MogleyC/Gentlman20211010/Etc/Doc/DM테크 블루투스 모듈/nrf52832_dm_rev3r1.pdf

## REVISION HISTORY

## REV1.0

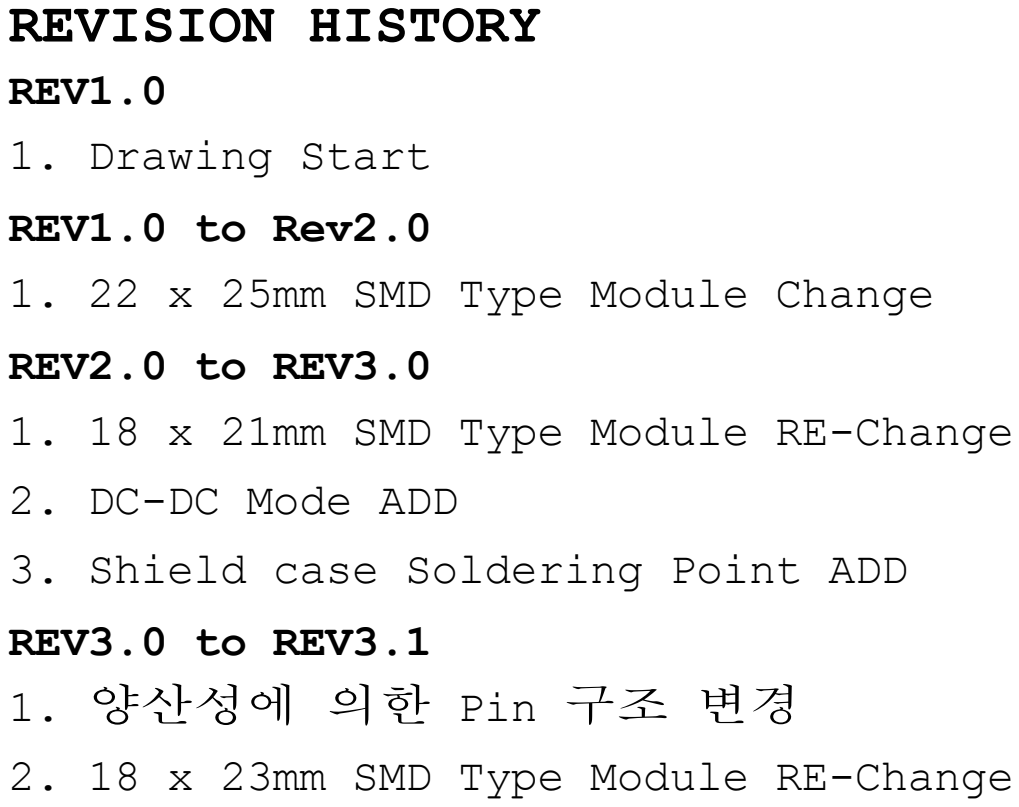
[picture p1: page 1]
Title; Size; Document Number; Rev; Date:; Sheet; <Doc>; nRF52832_DM Module; Tuesday, March 02, 2021

1. Drawing Start
REV1.0 to Rev2.0
1. 22 x 25mm SMD Type Module Change
REV2.0 to REV3.0
1. 18 x 21mm SMD Type Module RE-Change

2. DC-DC Mode ADD

3. Shield case Soldering Point ADD
REV3.0 to REV3.1
1. 양산성에 의한 Pin 구조 변경

2. 18 x 23mm SMD Type Module RE-Change

DMTech.Co.,Ltd.

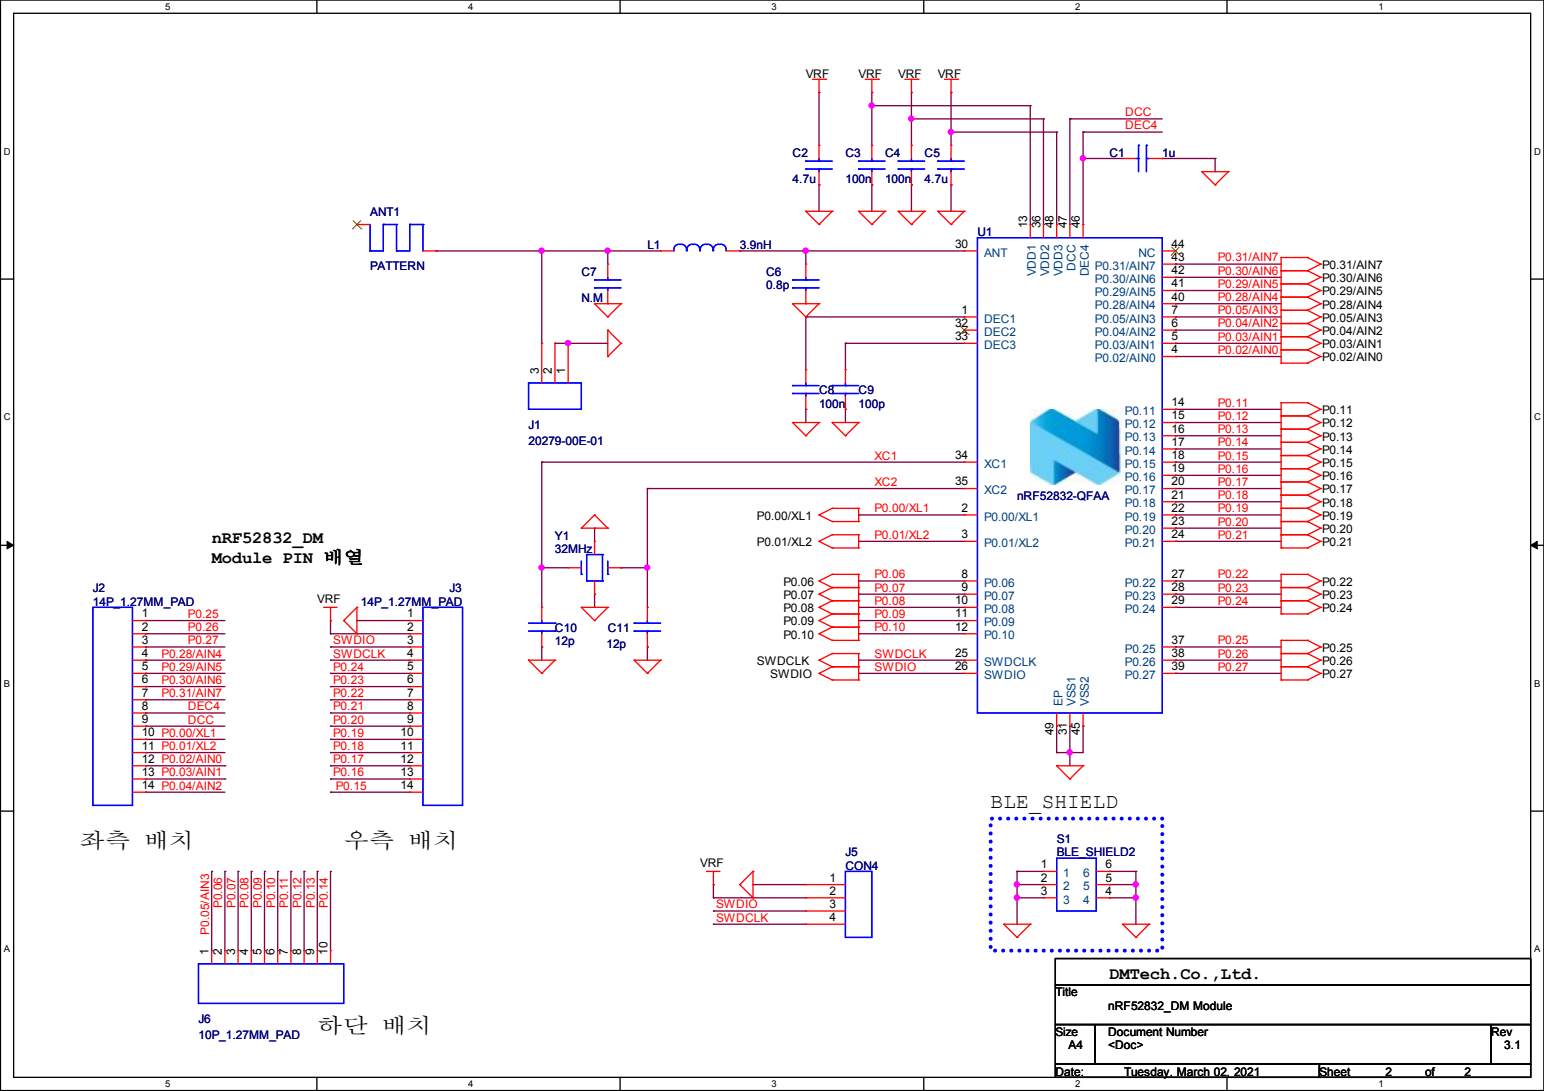
[picture p2: page 2]
