MogleyC/Gentlman20211010/Etc/Doc/nRF-DK/nRF52810 Reference circuitry.pdf

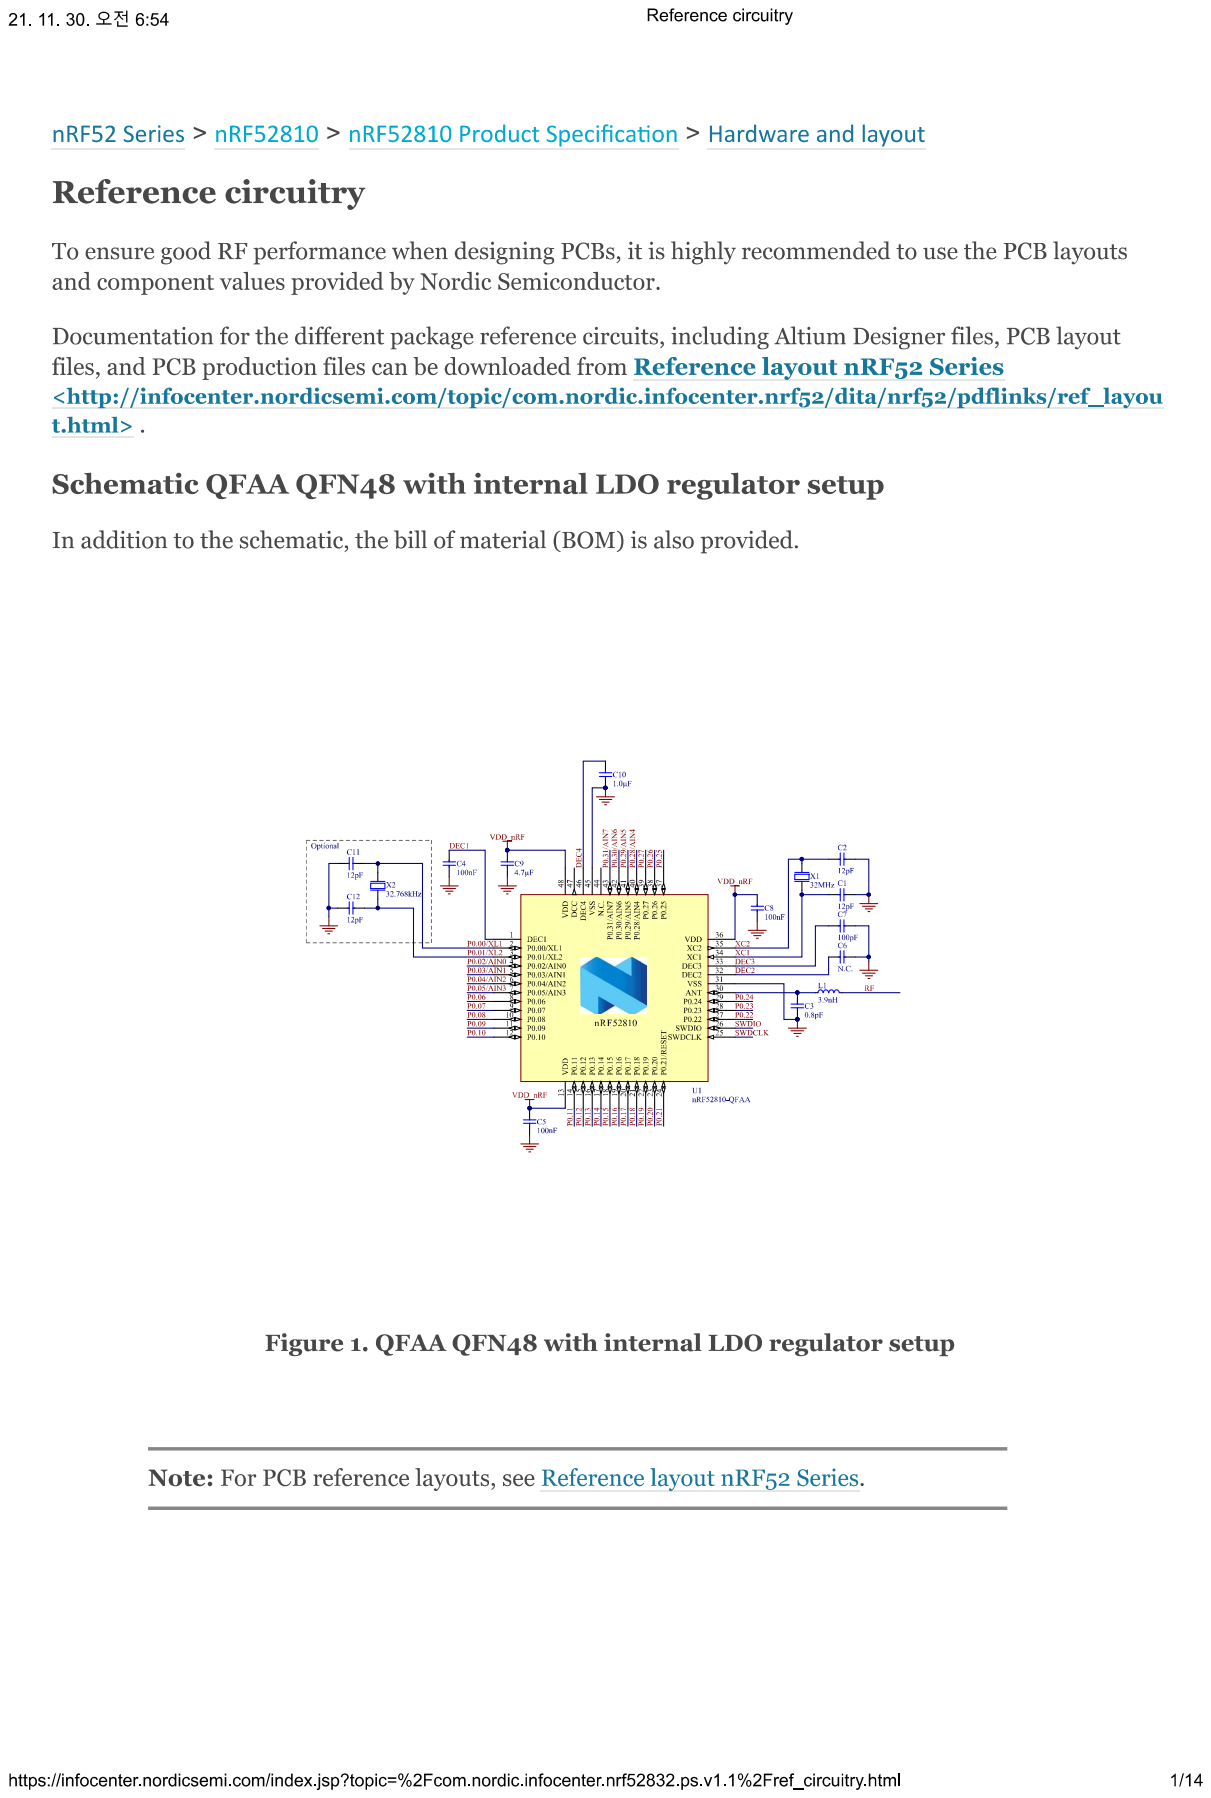
[picture p4: page 1]

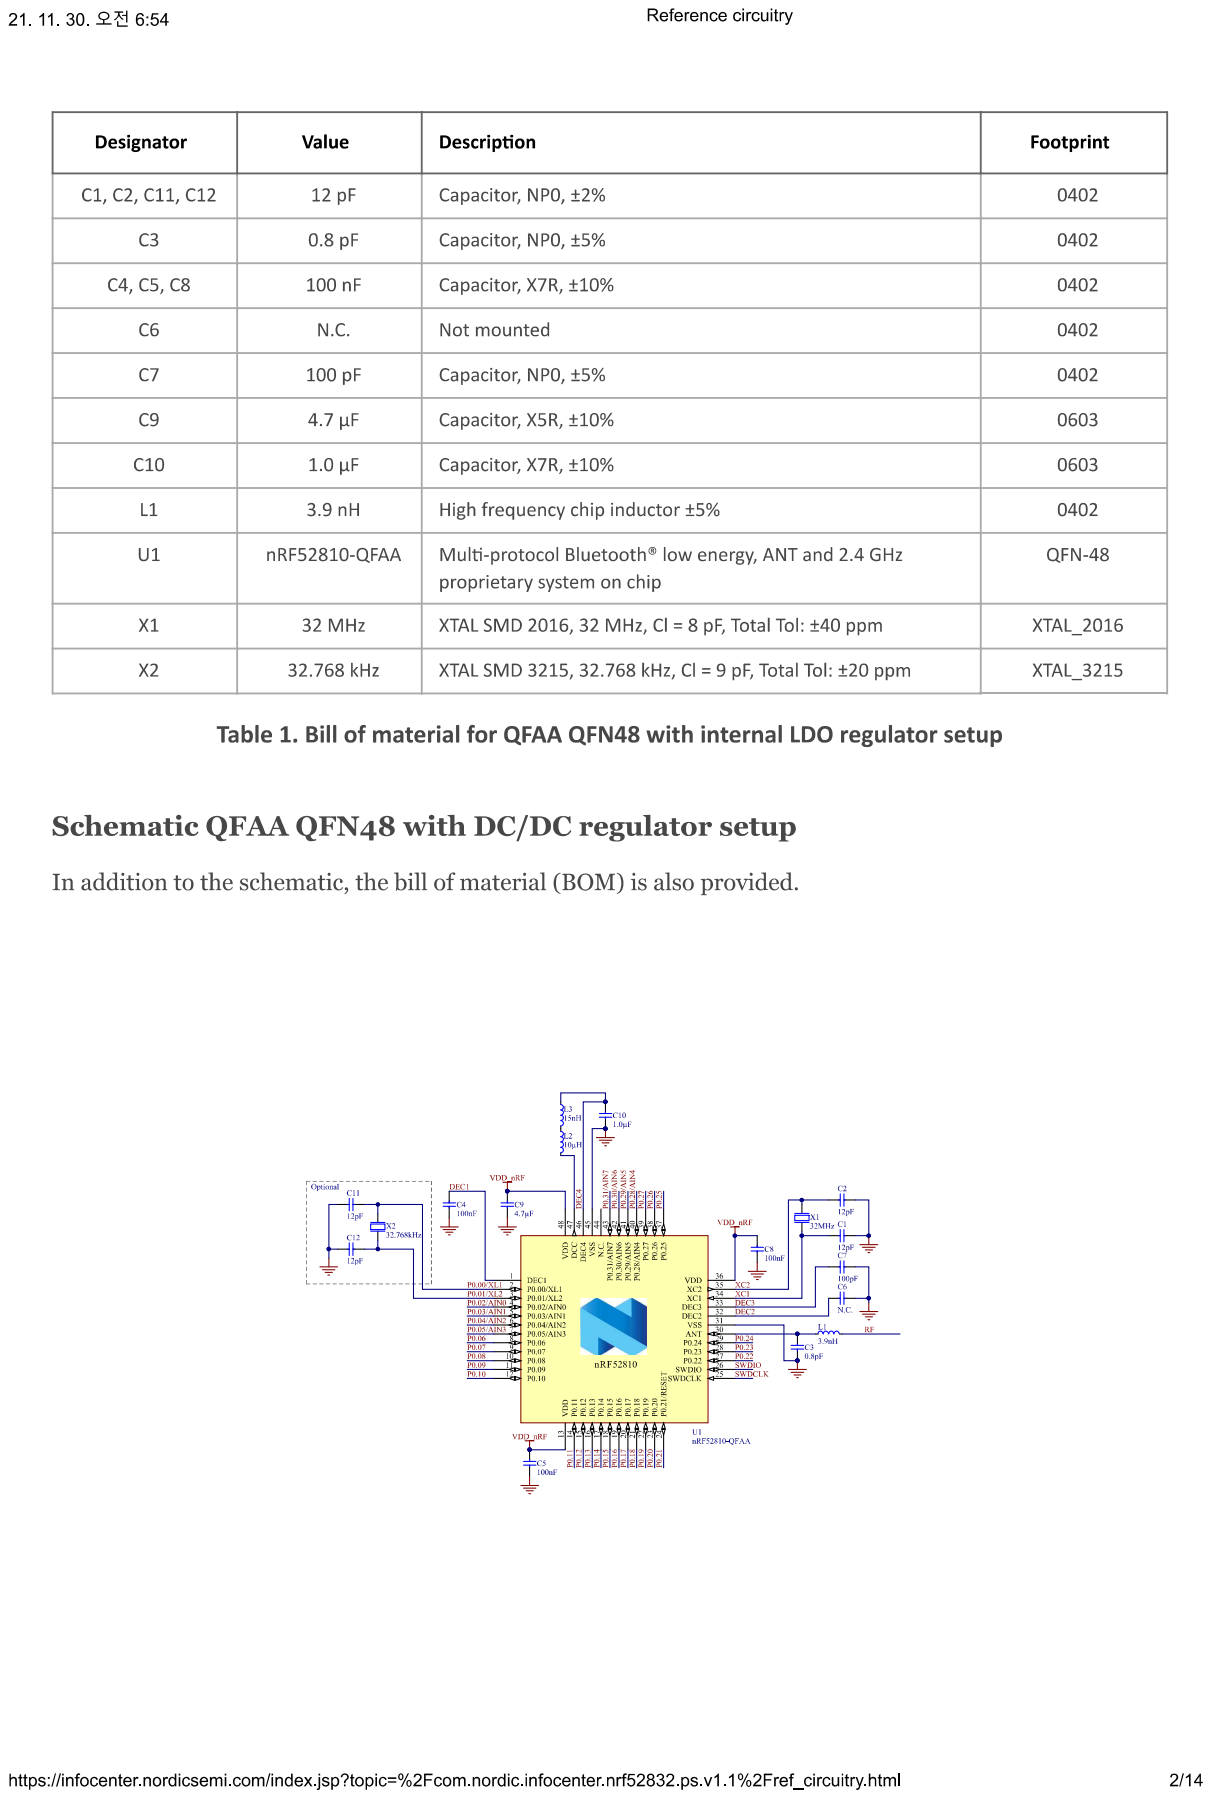
[picture p5: page 2]

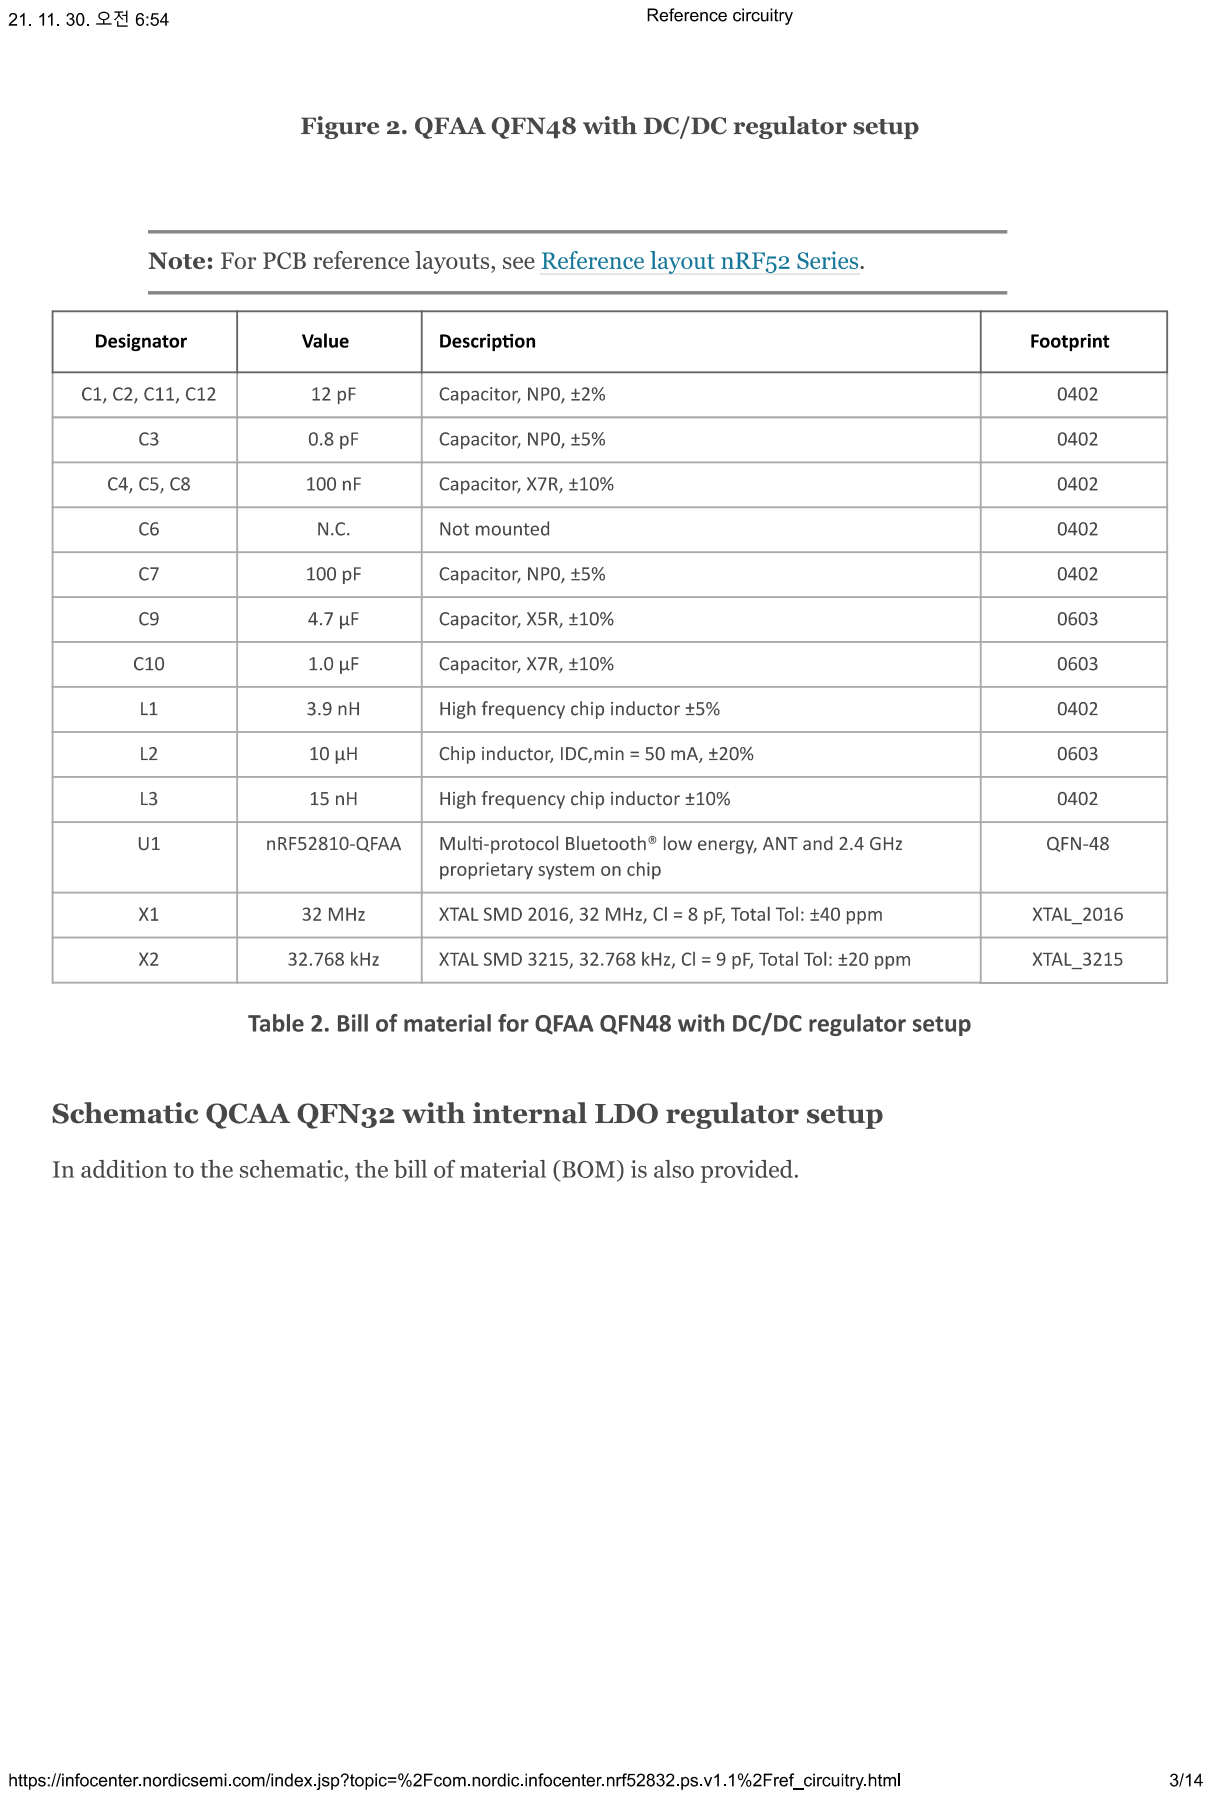
[picture p6: page 3]

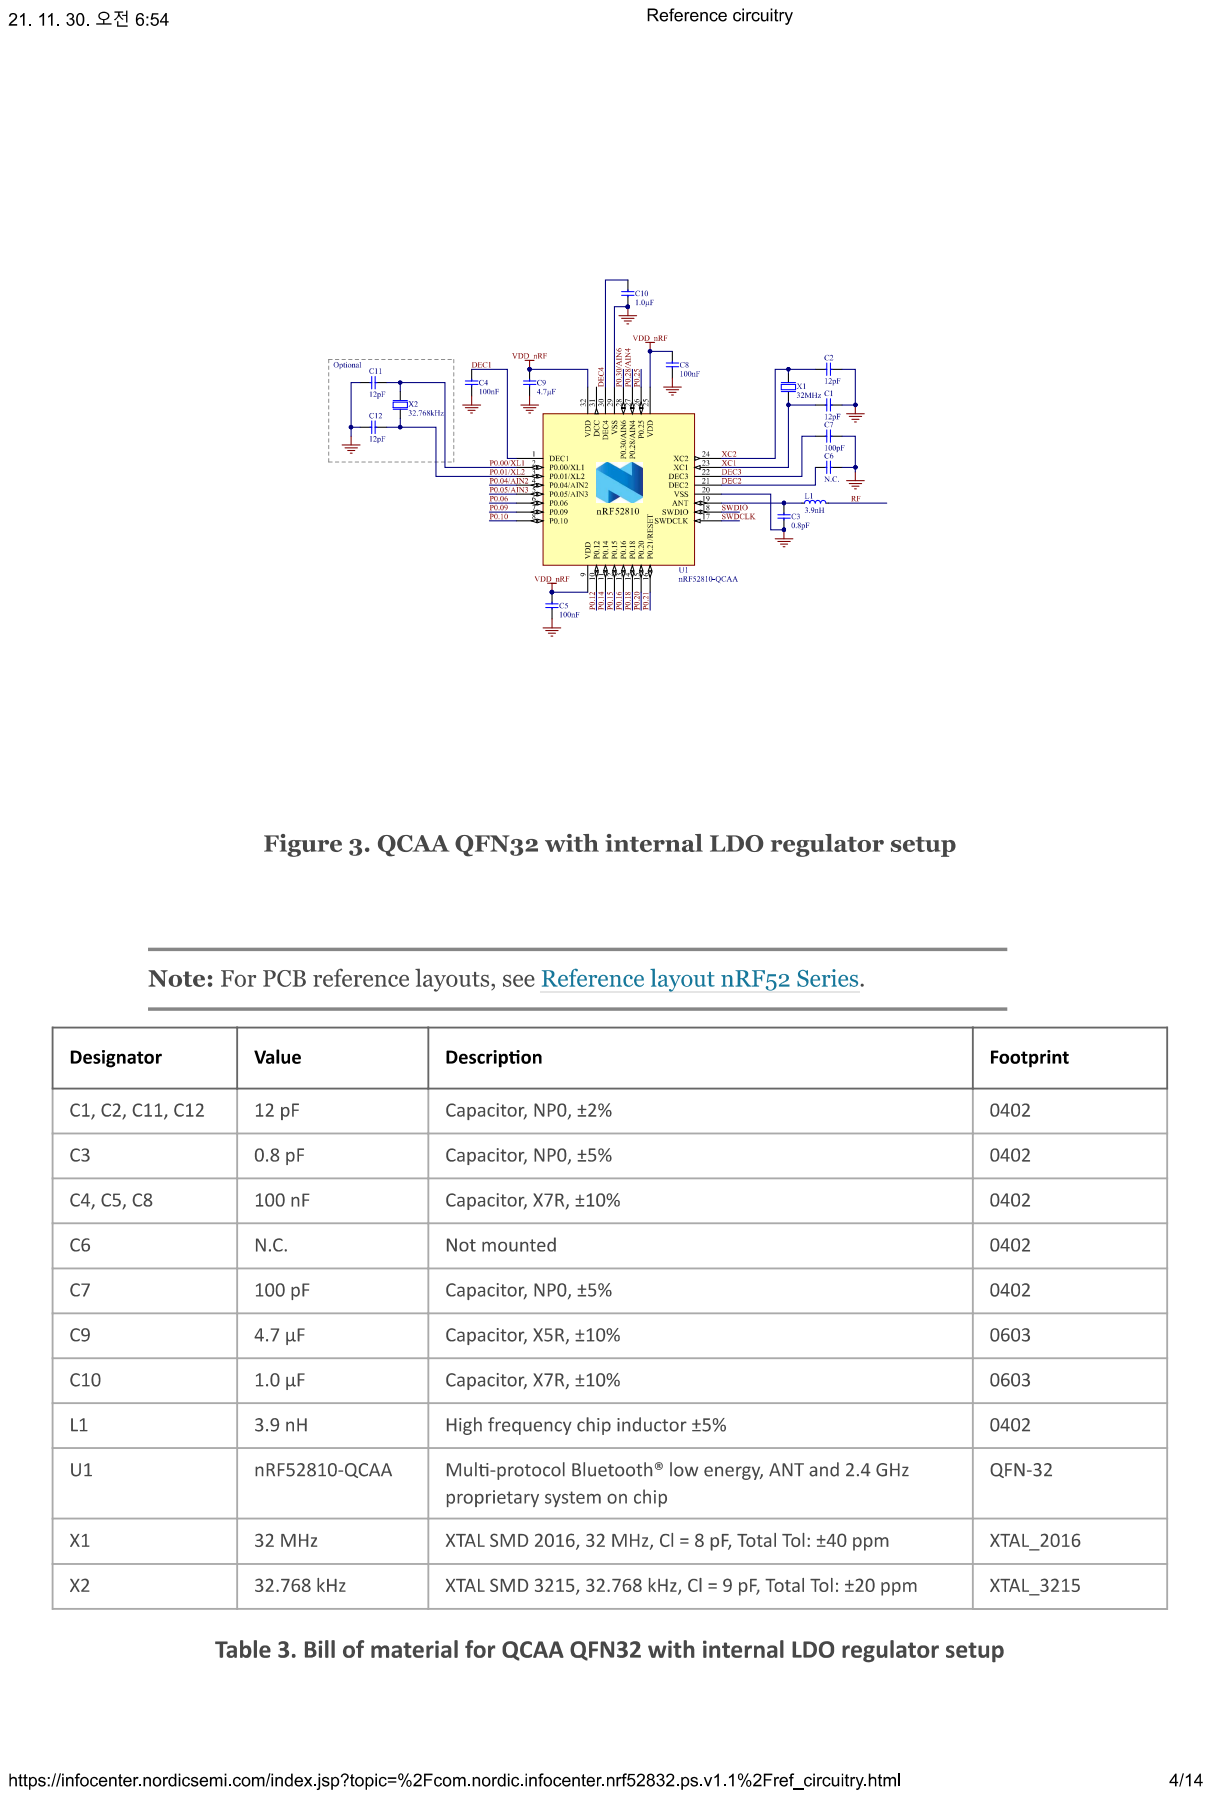
[picture p7: page 4]

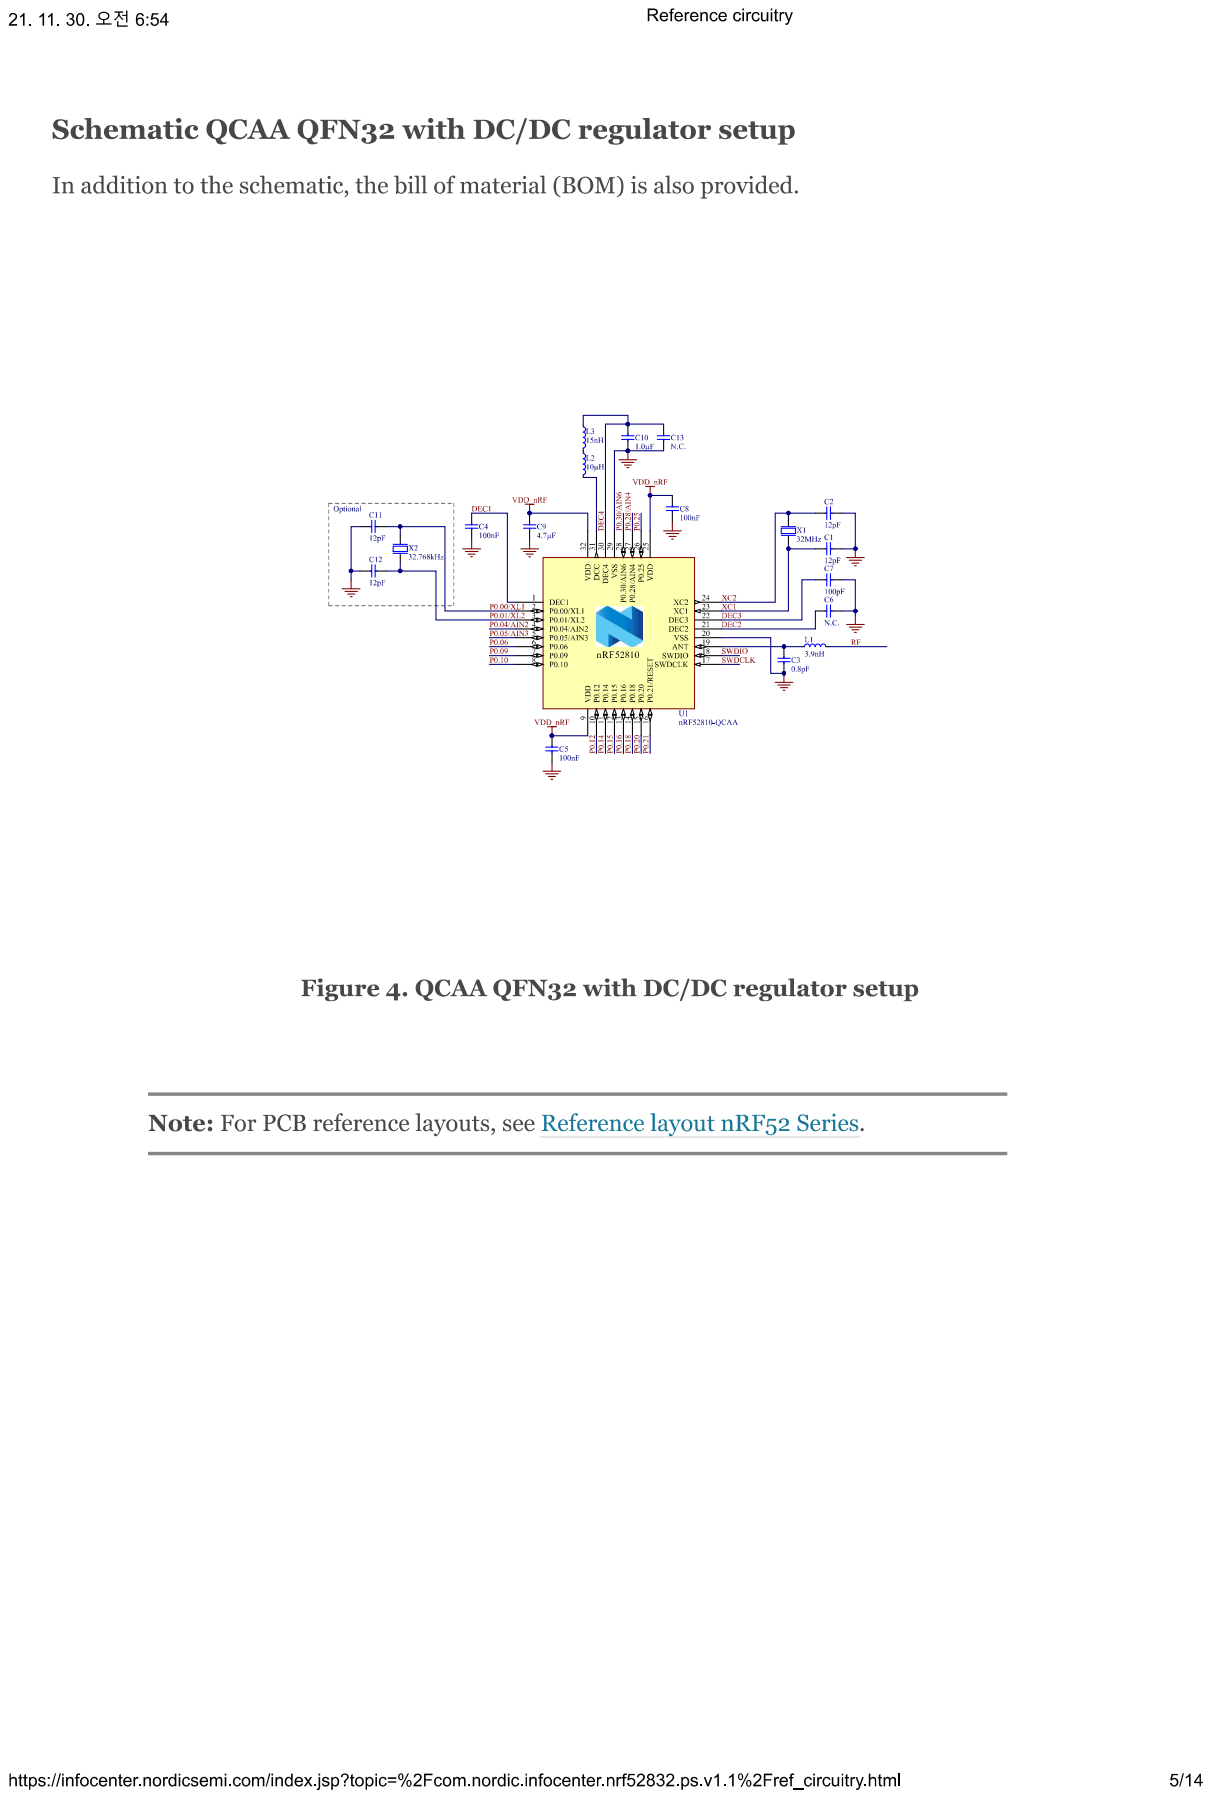
[picture p8: page 5]

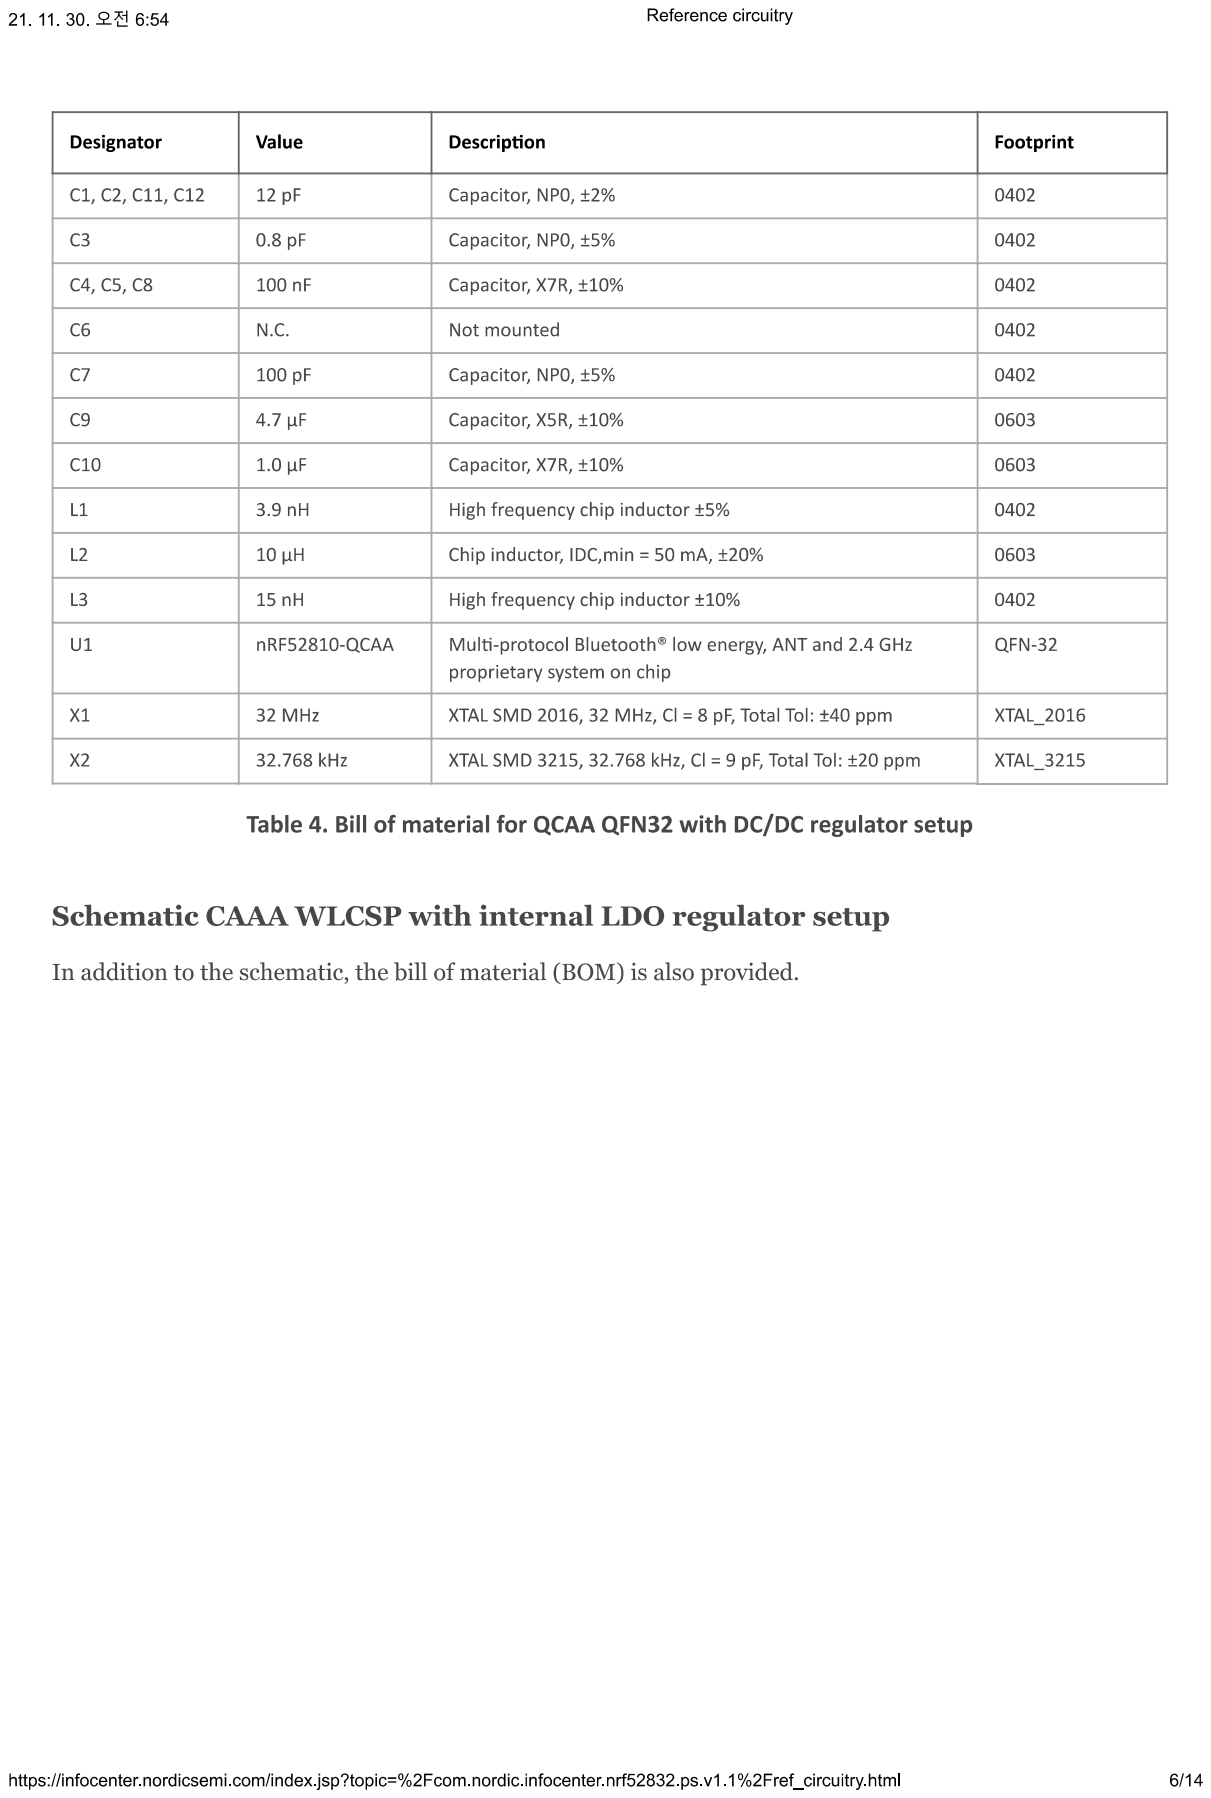
[picture p9: page 6]

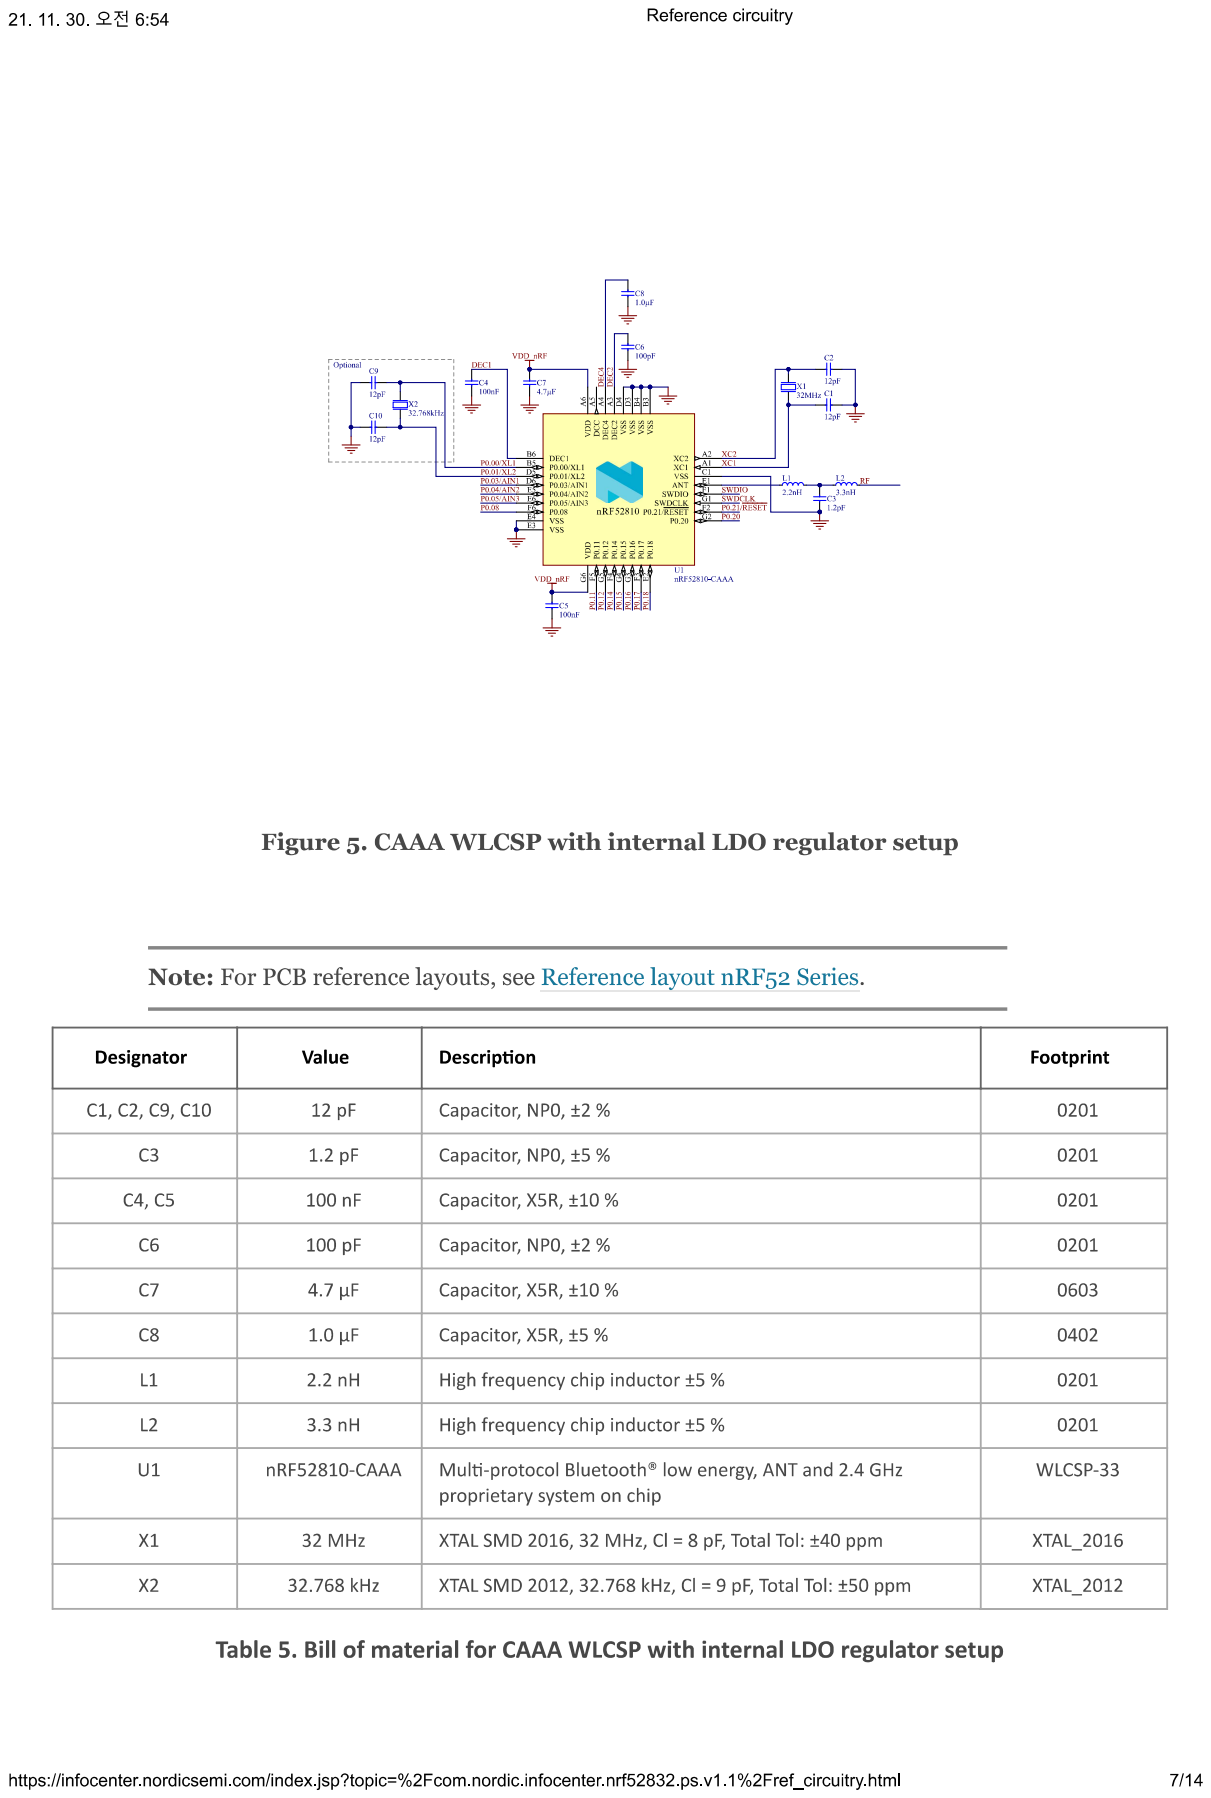
[picture p10: page 7]

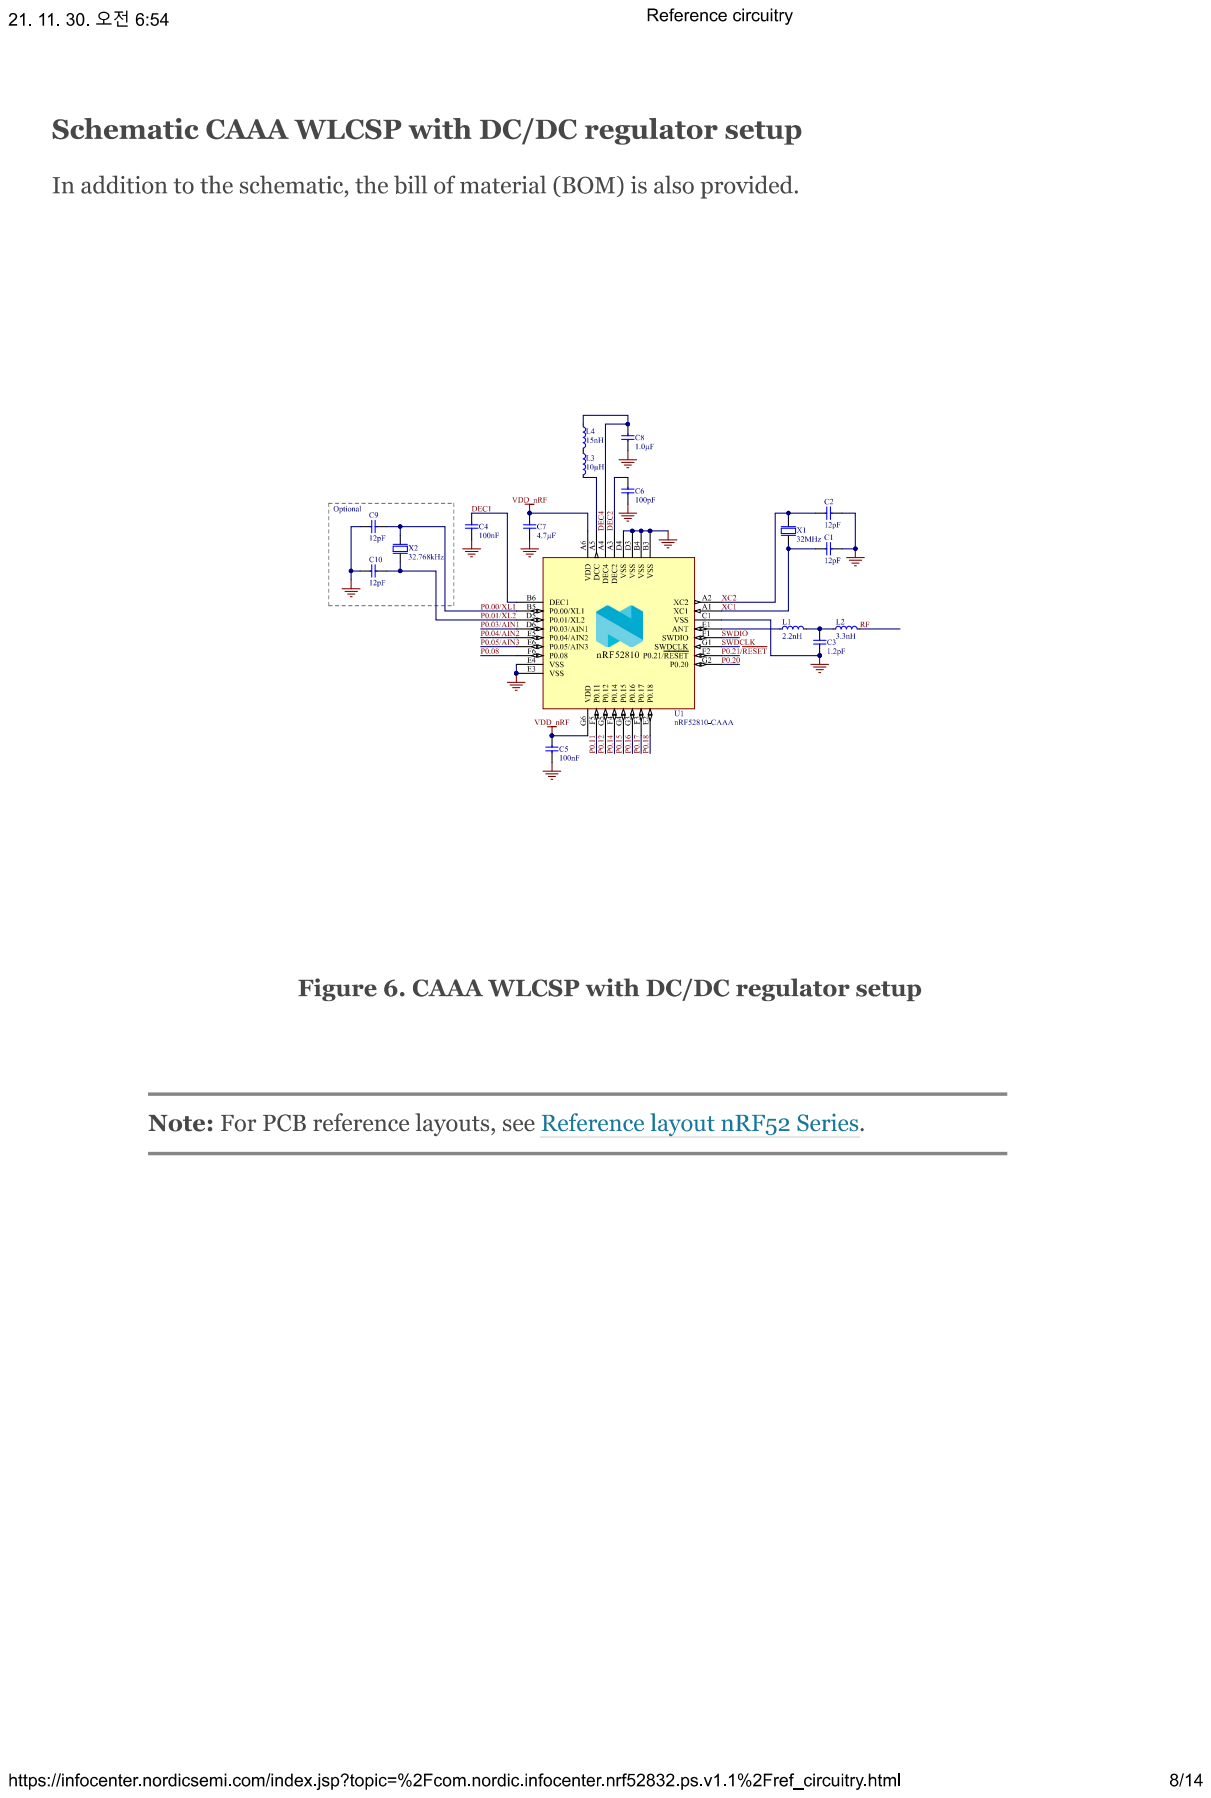
[picture p11: page 8]

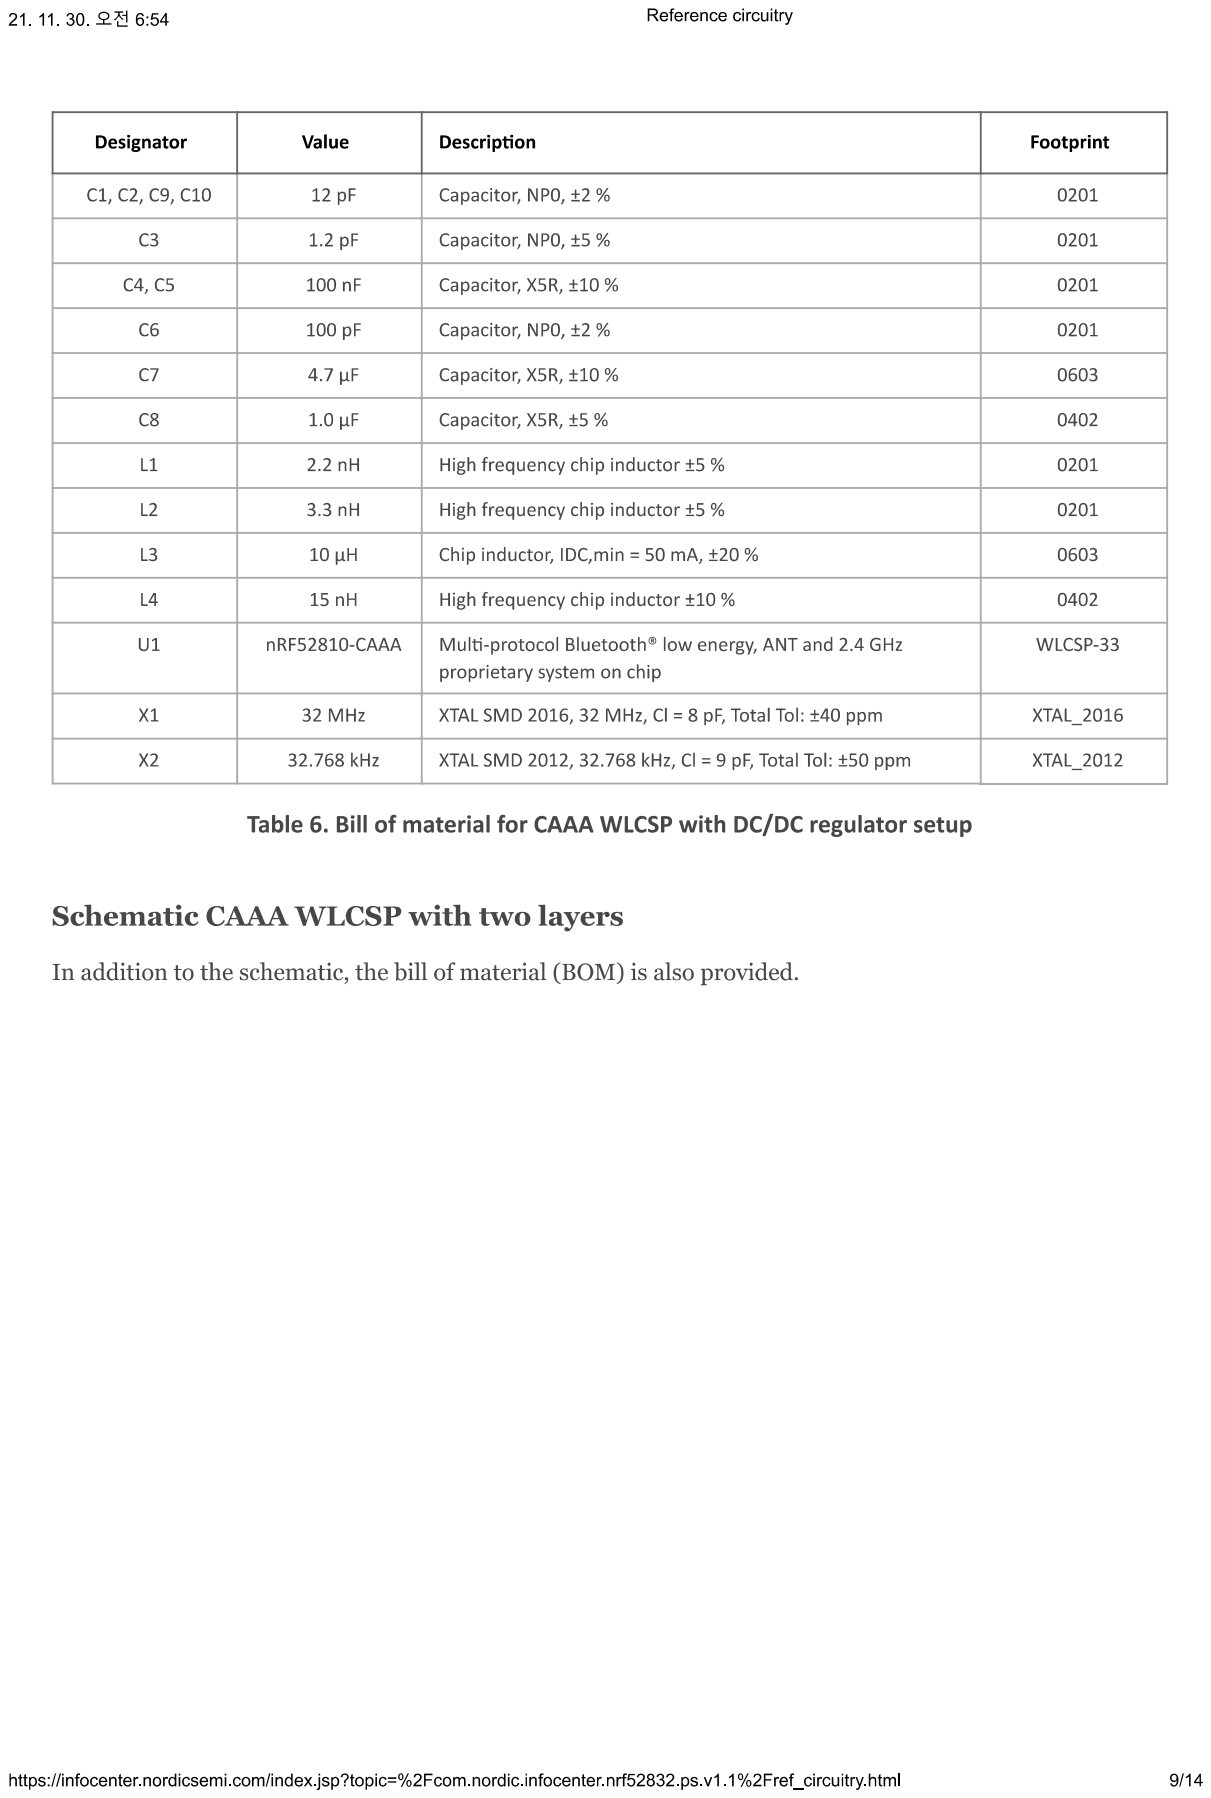
[picture p12: page 9]

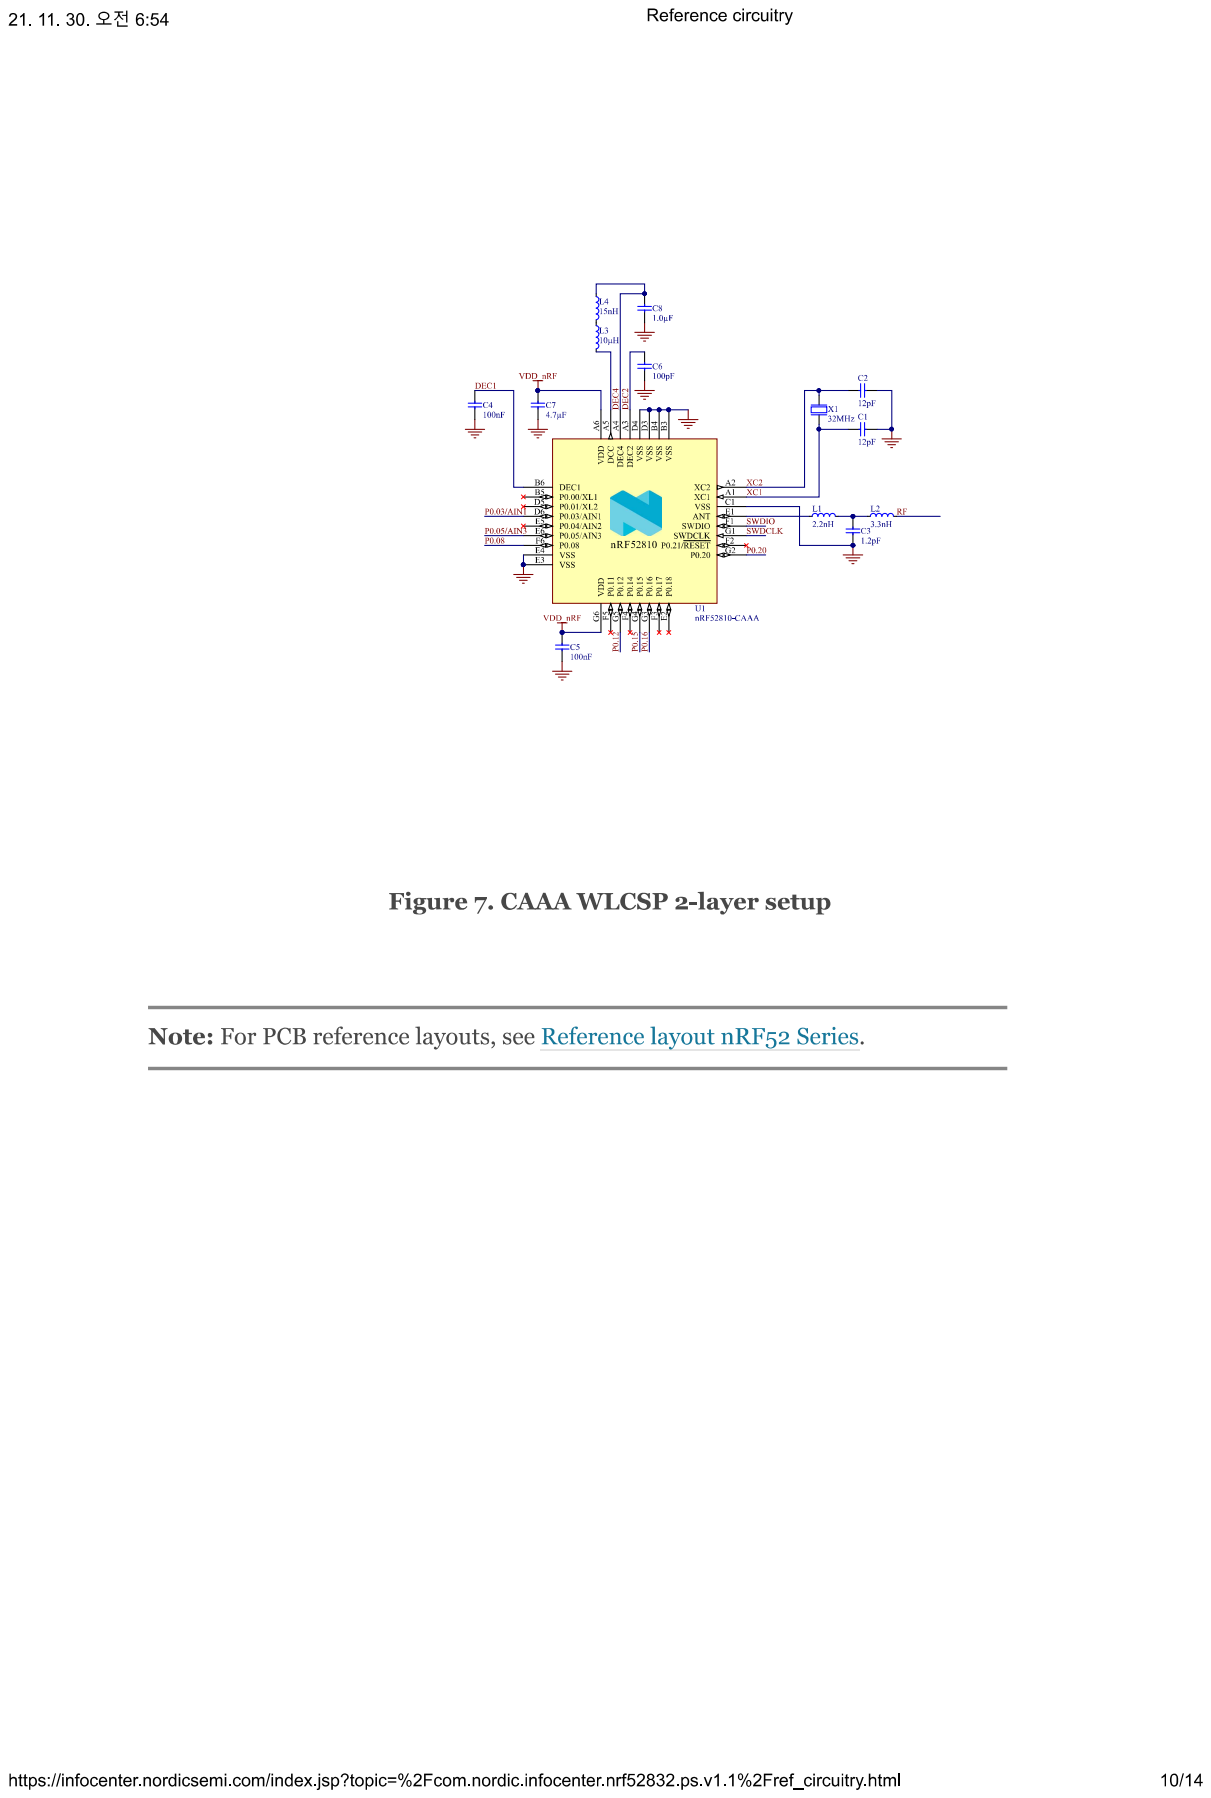
[picture p13: page 10]

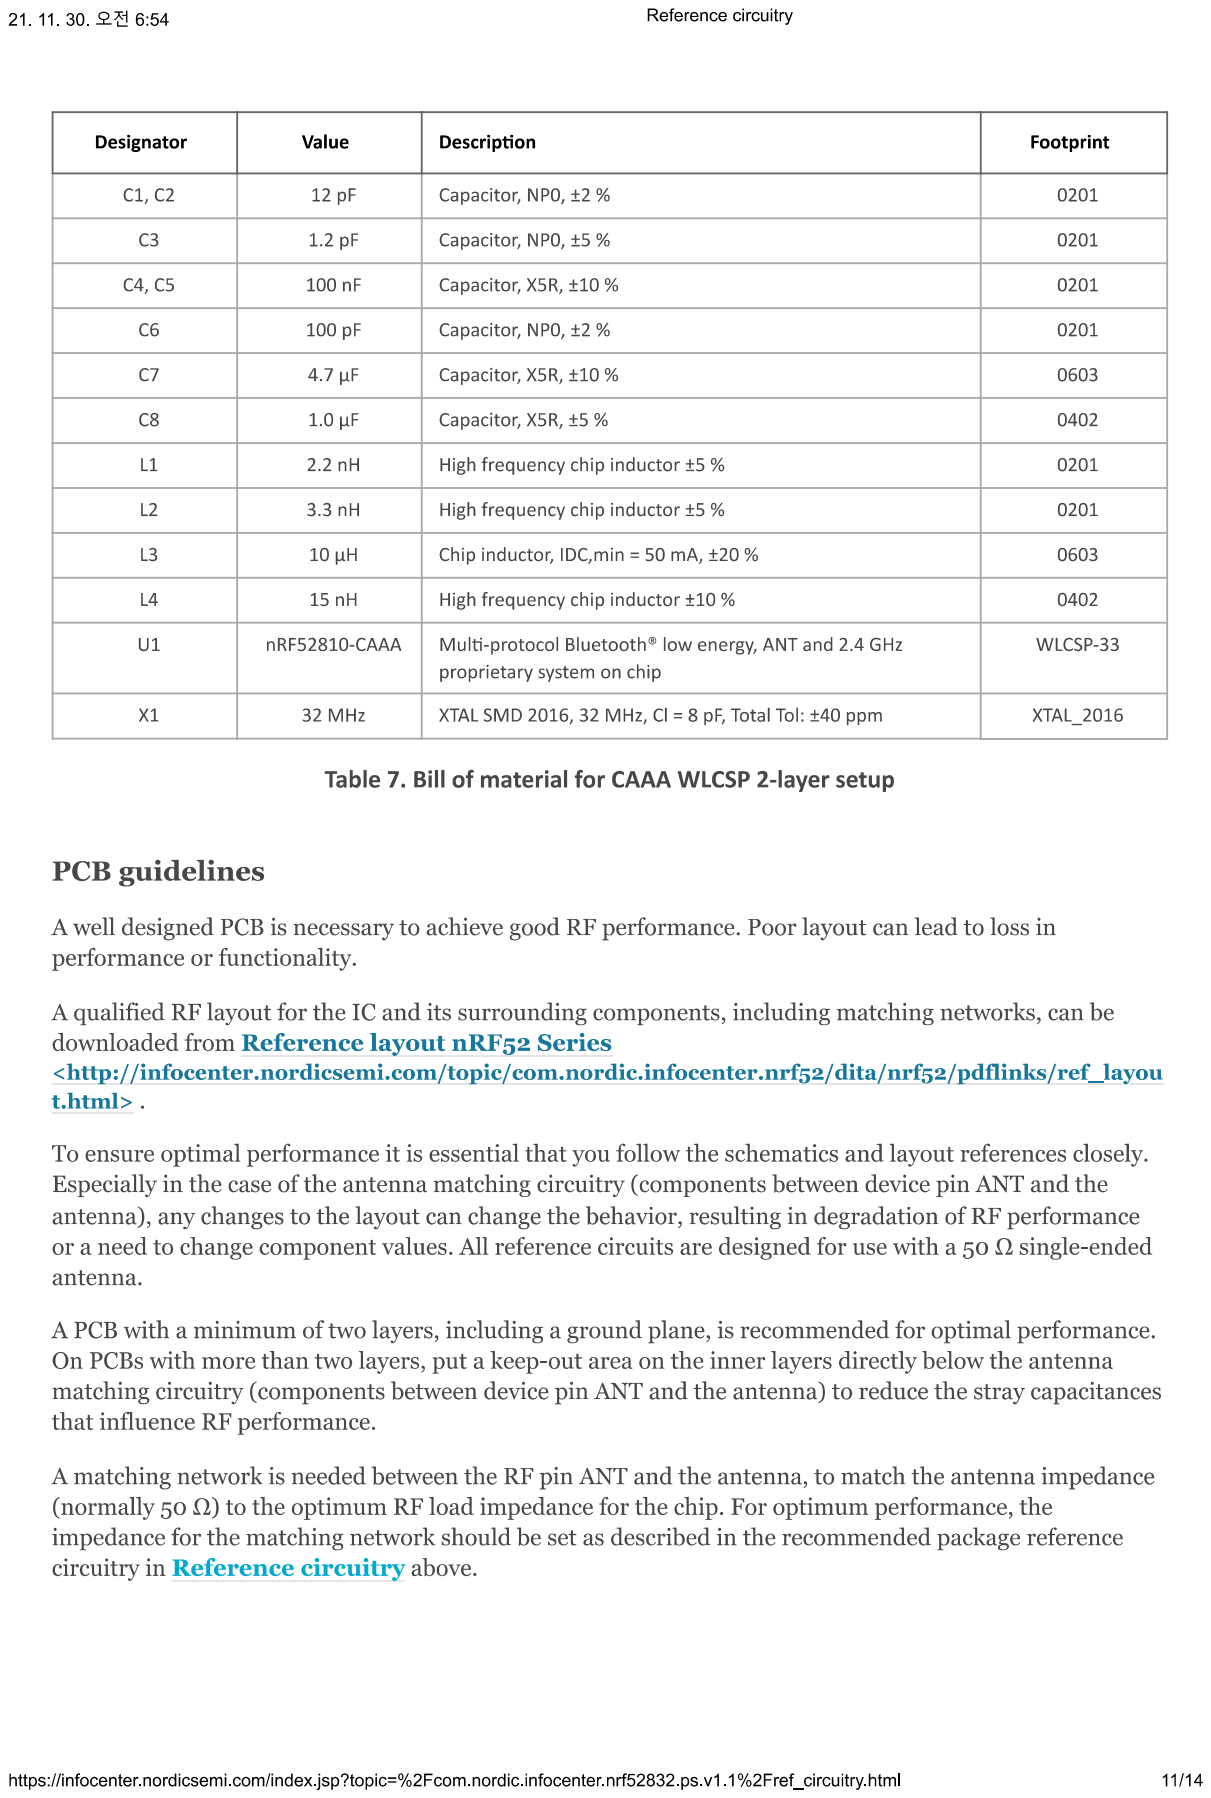
[picture p14: page 11]

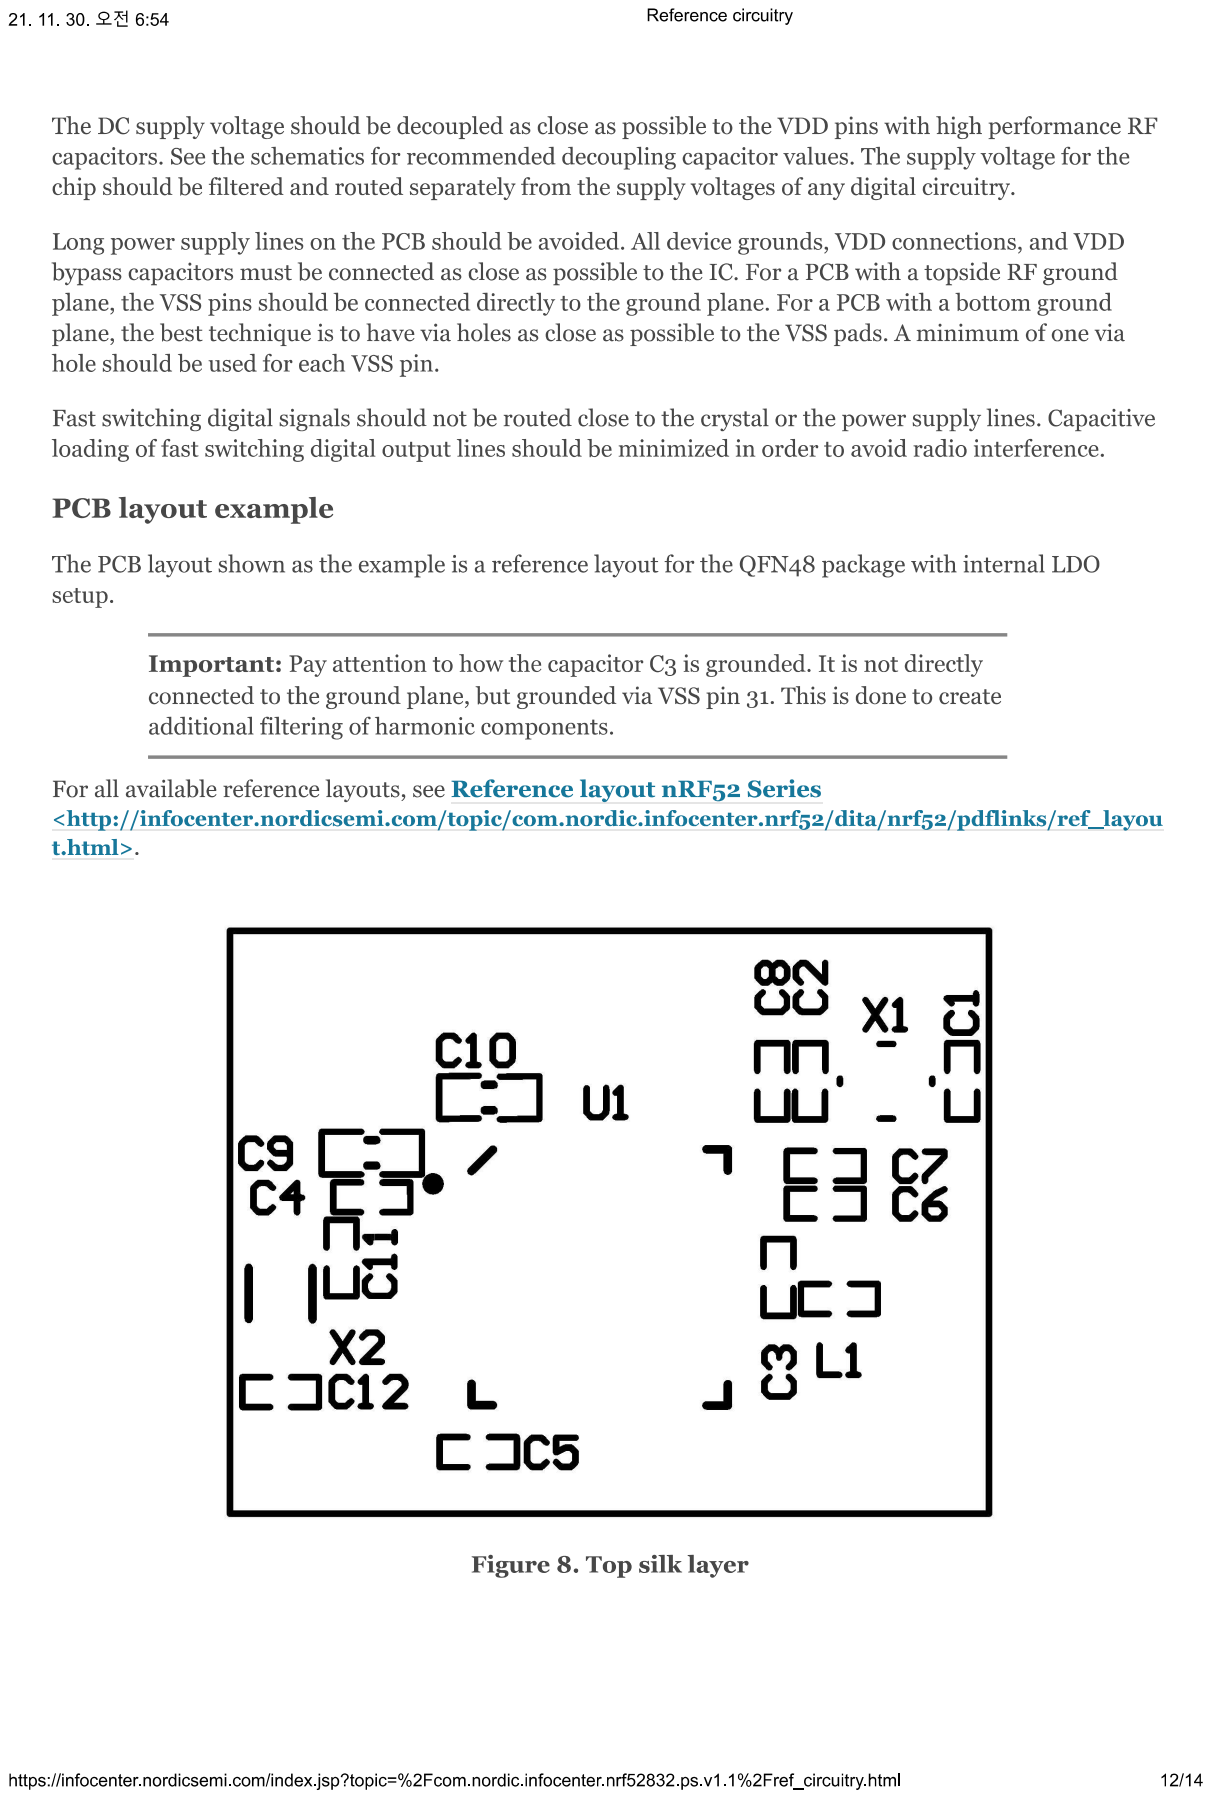
[picture p15: page 12]

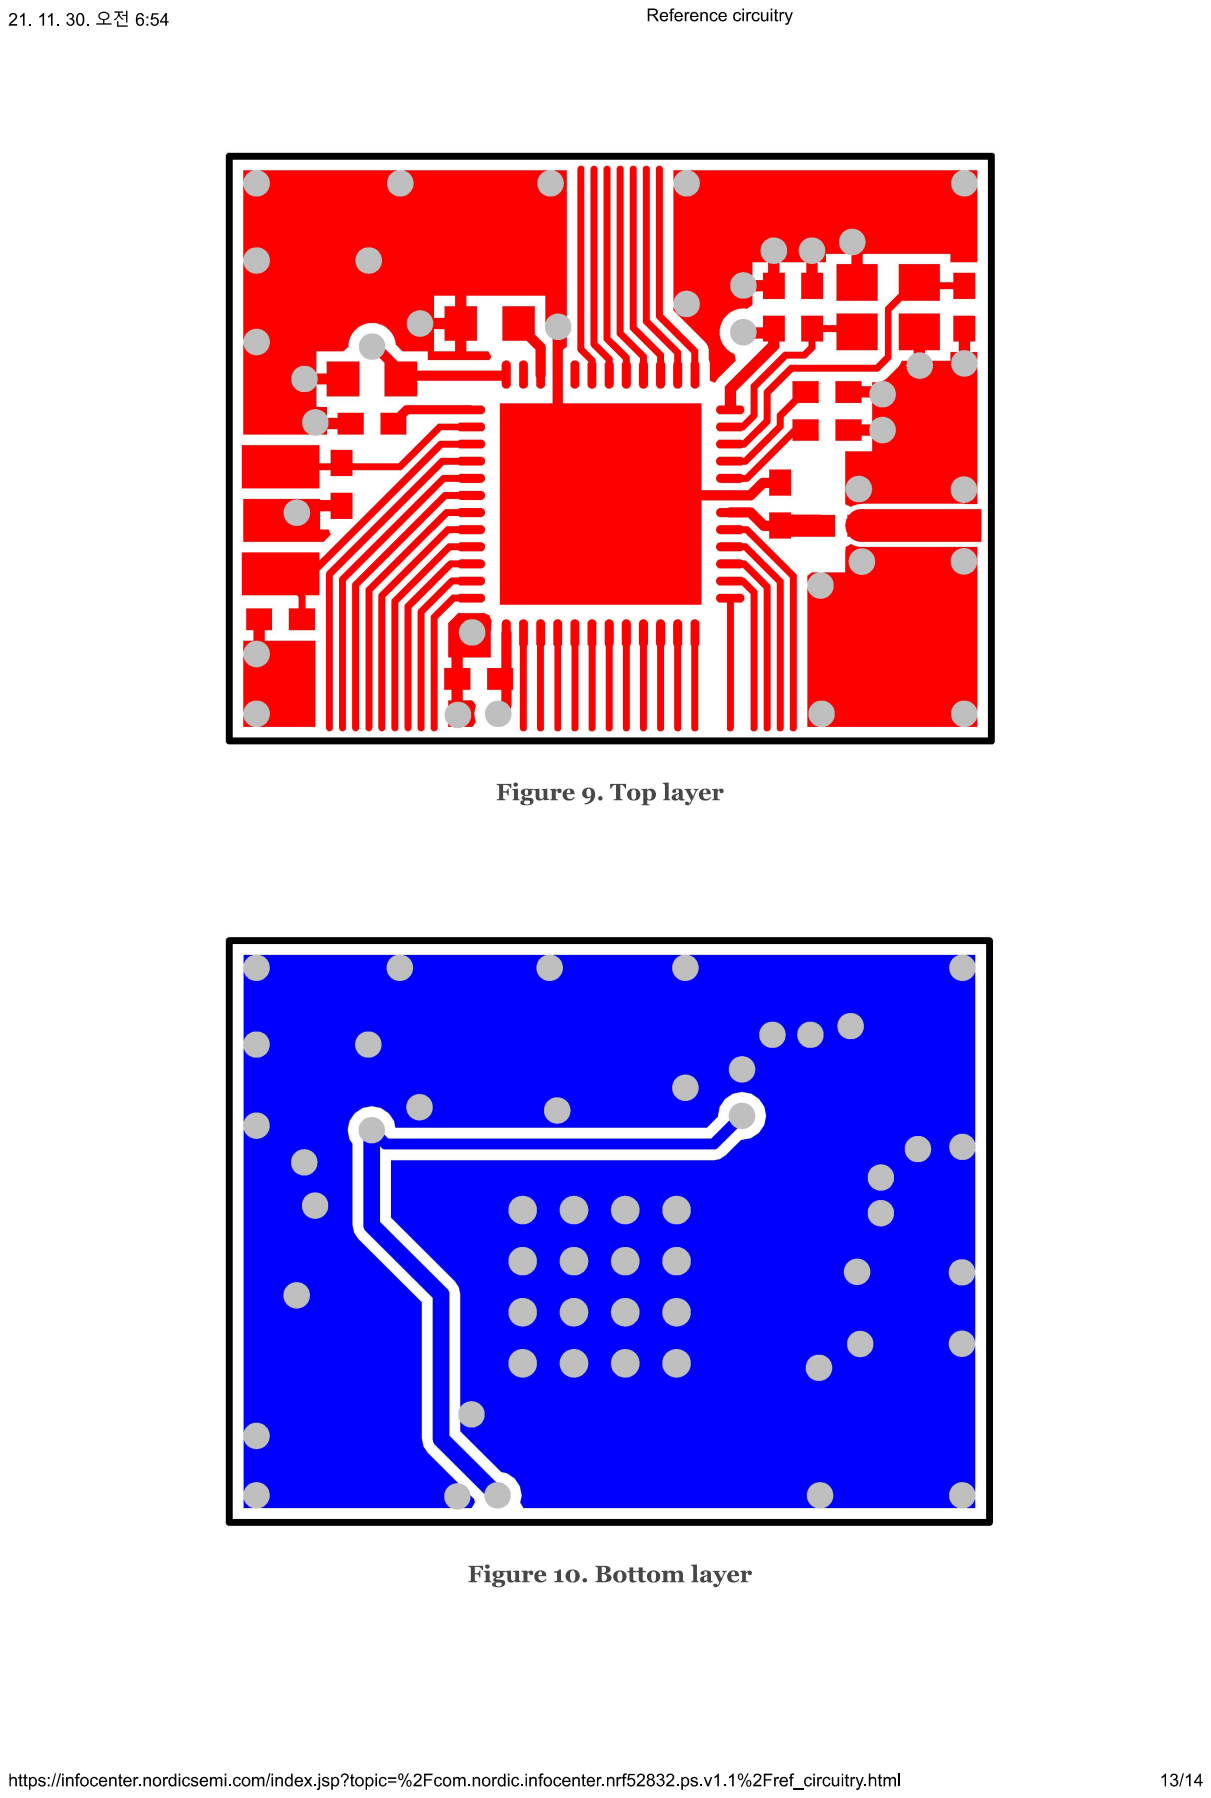
[picture p16: page 13]

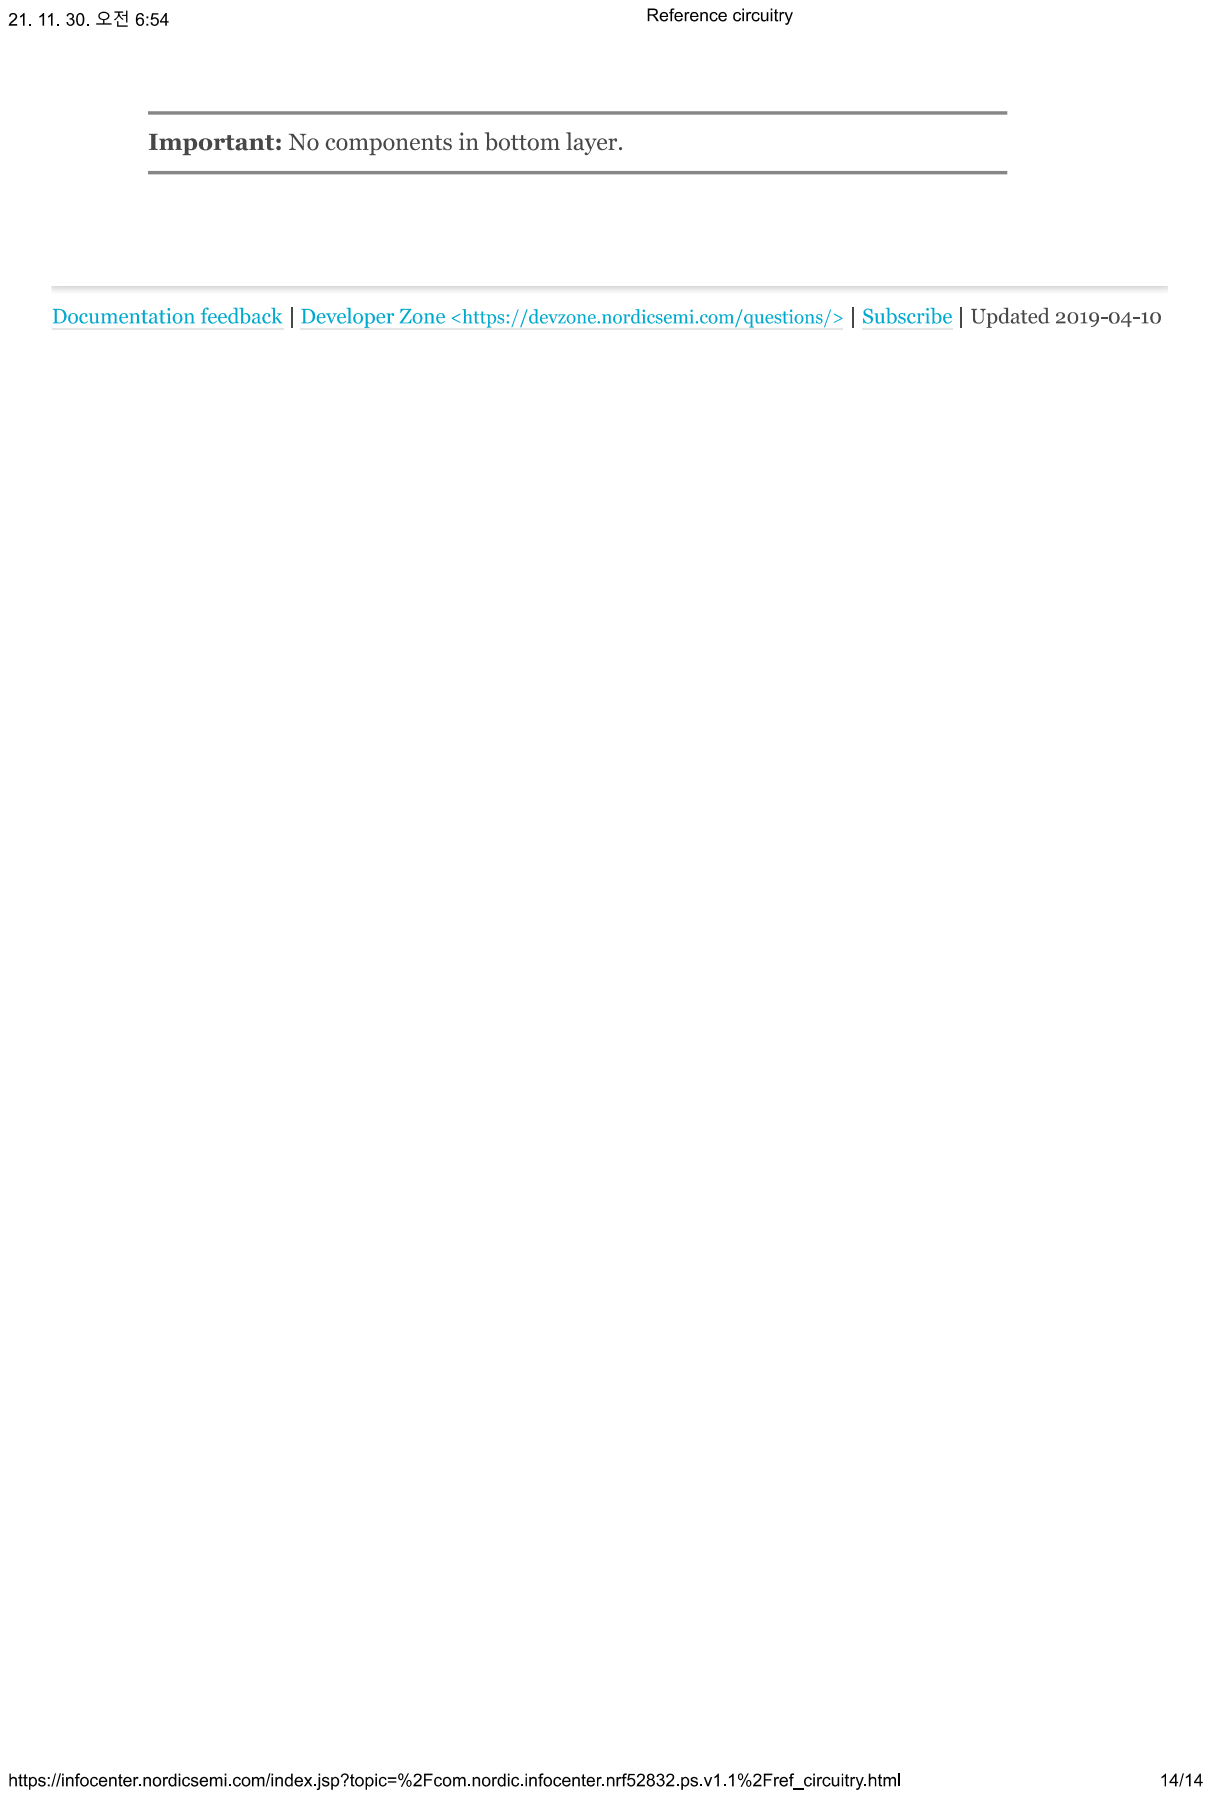
[picture p17: page 14]
