MogleyC/Gentlman20211010/KiCAD/KiCAD_Gentlman_V5.3/Dataseets/V5.2/201228 CPP-093AB(demo2).PDF

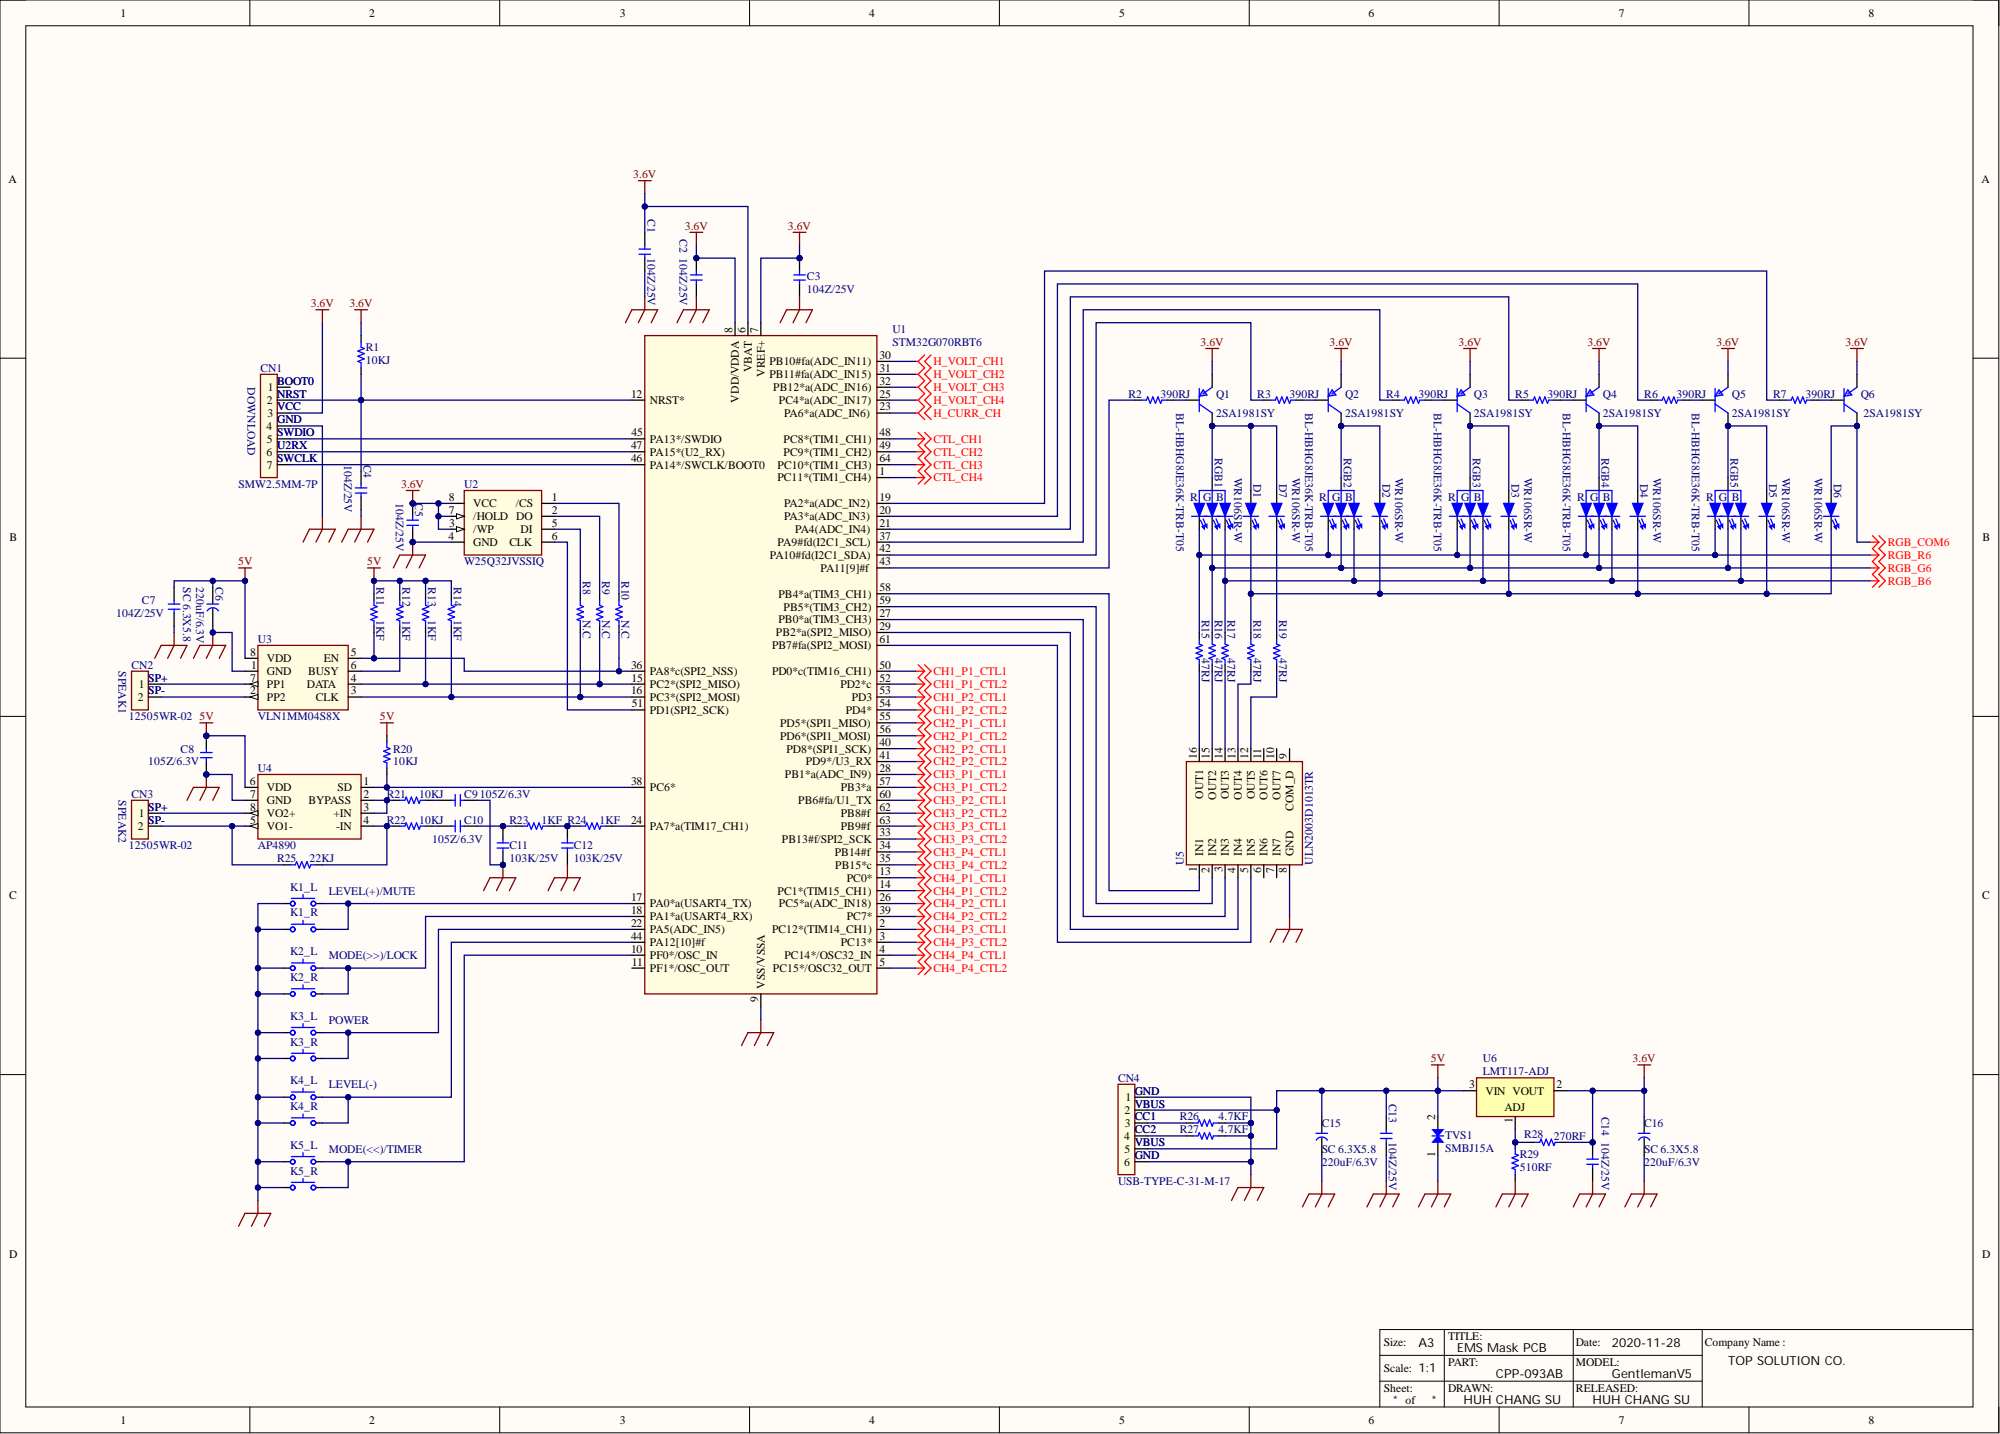
[picture p18: page 1]

U 2RX | | 4
K | 4 6

5 9
2 7
2 9
6 1

1 8 | | 3 9
2 2 | | 2
4 4 | | 3

D E(>>)/ L OCK | | 1 0

R2 6 4.7 KF
R2 4.7 | KF

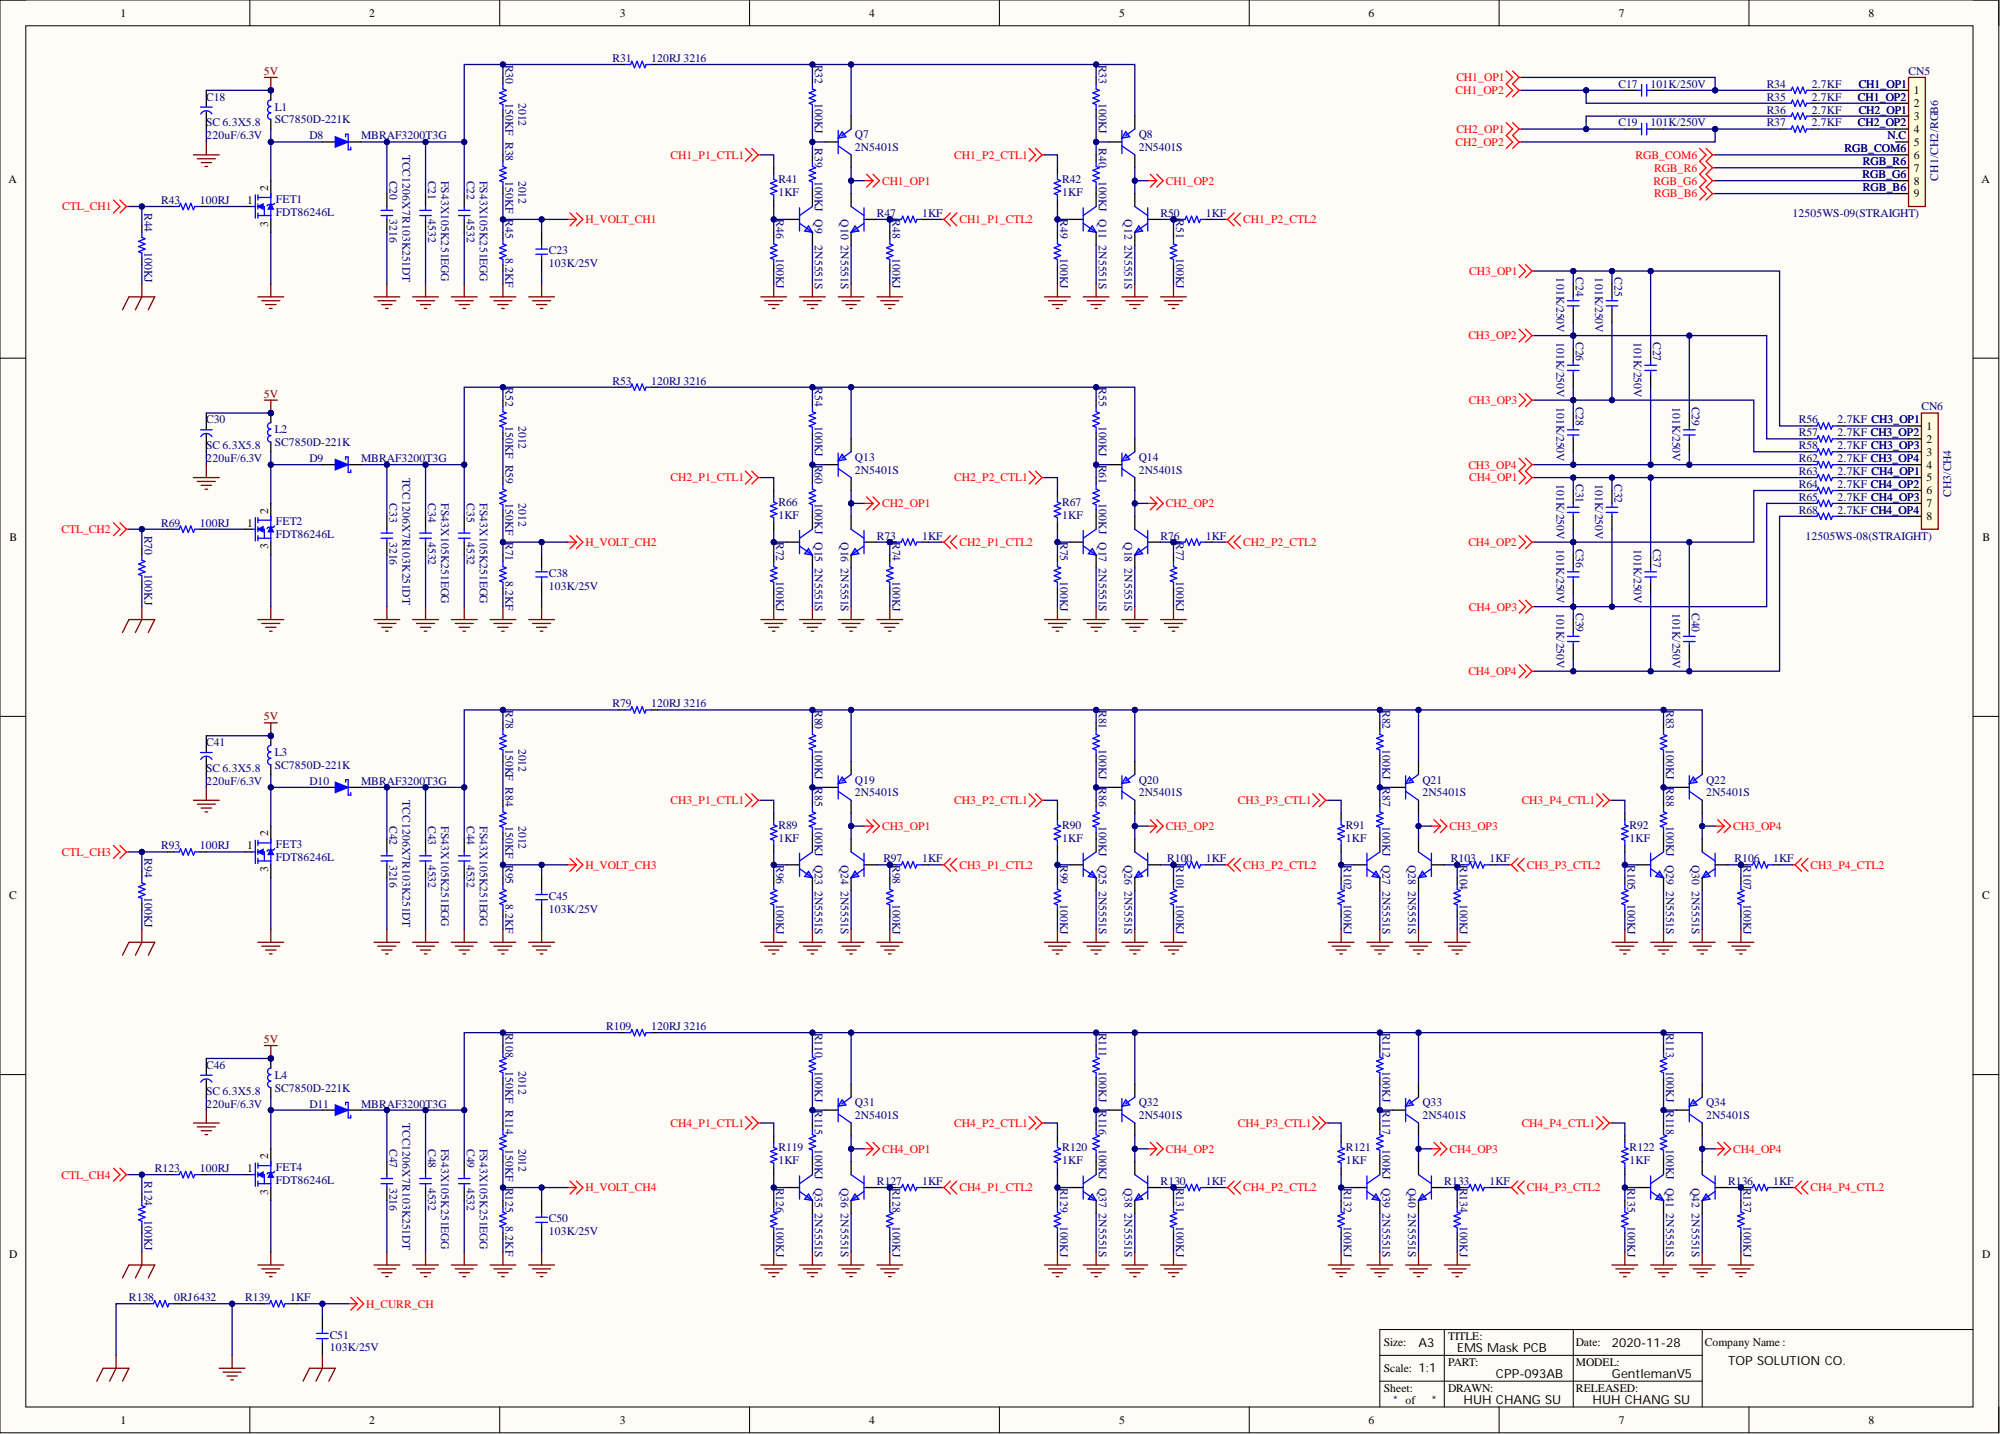
[picture p19: page 2]

R5
R6
