MogleyC/Gentlman20211010/Ses/G5.3B_nRF/SRC/Module_Radio.c

#include "Module_Radio.h"

#include <stdbool.h>
//#include <stdlib.h>
//#include <string.h>

#include "board_config.h"
#include "nrf.h"

#include "radio_config.h"
//#include "Module_Uart.h"
//#include "nrf_drv_gpiote.h"
//#include "nrf_drv_systick.h"

static uint32_t packet = 0;

void radio_Init()
{
	radio_configure();

	NRF_RADIO->PACKETPTR = (uint32_t)&packet; // Set payload pointer
}

void radio_send_packet(uint32_t SetPacket)
{
	packet = SetPacket;

	// send the packet:
	NRF_RADIO->EVENTS_READY = 0U;
	NRF_RADIO->TASKS_TXEN = 1;
	while (NRF_RADIO->EVENTS_READY == 0U) {}

	NRF_RADIO->EVENTS_END = 0U;
	NRF_RADIO->TASKS_START = 1U;
	while (NRF_RADIO->EVENTS_END == 0U) {}

	NRF_RADIO->EVENTS_DISABLED = 0U;
	NRF_RADIO->TASKS_DISABLE = 1U; // Disable radio
	while (NRF_RADIO->EVENTS_DISABLED == 0U) {}
}

uint32_t radio_read_packet()
{
	uint32_t result = 0;

	NRF_RADIO->EVENTS_READY = 0U;
	NRF_RADIO->TASKS_RXEN = 1U; // Enable radio and wait for ready
	while (NRF_RADIO->EVENTS_READY == 0U) {}
	NRF_RADIO->EVENTS_END = 0U;
	NRF_RADIO->TASKS_START = 1U; // Start listening and wait for address received event
	while (NRF_RADIO->EVENTS_END == 0U) {}

	if (NRF_RADIO->CRCSTATUS == 1U)
	{
		result = packet;
	}

	NRF_RADIO->EVENTS_DISABLED = 0U;
	NRF_RADIO->TASKS_DISABLE = 1U; // Disable radio
	while (NRF_RADIO->EVENTS_DISABLED == 0U) {}

	return result;
}

void rssiTx_ProgressExample()
{
	radio_Init();

	uint8_t NowTxPacket = 0;
	while (1)
	{
		radio_send_packet(NowTxPacket);

		++NowTxPacket;
		if (NowTxPacket == 64)
		{
			NRF_RADIO->FREQUENCY++;
			if (NRF_RADIO->FREQUENCY == 80)
			{
				NRF_RADIO->FREQUENCY = 0;
			}

			NowTxPacket = 0;
		}
	}
}

#include "Module_GPIO.h"
#include "nrf_drv_systick.h"
void radioiTx_ProgressExample()
{
	gpioe_init();
	gpioe_output_set(LED_1_PIN_NUMBER, true);
	nrf_drv_systick_init();
	
	radio_Init();

	while (1)
	{
		for (uint8_t i = 0; i < 4; ++i)
		{
			radio_send_packet(i);
			nrf_drv_gpiote_out_toggle(LED_1_PIN_NUMBER);
			nrf_drv_systick_delay_ms(500);
		}
	}
}

#include "Module_GPIO.h"
void radioiRx_ProgressExample()
{
	gpioe_init();
	gpioe_output_set(LED_1_PIN_NUMBER, true);
	gpioe_output_set(LED_2_PIN_NUMBER, true);
	
	radio_Init();

	while (1)
	{
		uint8_t tmpPacket = radio_read_packet();

		switch (tmpPacket)
		{
			case 0:
				nrf_drv_gpiote_out_set(LED_1_PIN_NUMBER);
				nrf_drv_gpiote_out_clear(LED_2_PIN_NUMBER);
				break;

			case 1:
				nrf_drv_gpiote_out_clear(LED_1_PIN_NUMBER);
				nrf_drv_gpiote_out_set(LED_2_PIN_NUMBER);
				break;

			case 2:
				nrf_drv_gpiote_out_clear(LED_1_PIN_NUMBER);
				nrf_drv_gpiote_out_clear(LED_2_PIN_NUMBER);
				break;

			case 3:
				nrf_drv_gpiote_out_set(LED_1_PIN_NUMBER);
				nrf_drv_gpiote_out_set(LED_2_PIN_NUMBER);
				break;
		}
	}
}
