MogleyC/Gentlman20211010/Iar/GentlemanV5.3B/Src/ringbuf.c

#include "ringbuf.h"
/*---------------------------------------------------------------------------*/
void
ringbuf_init(struct ringbuf *r, uint8_t *dataptr, uint8_t size)
{
  r->data = dataptr;
  r->mask = size - 1;
  r->put_ptr = 0;
  r->get_ptr = 0;
}
/*---------------------------------------------------------------------------*/
int
ringbuf_put(struct ringbuf *r, uint8_t c)
{
  /* Check if buffer is full. If it is full, return 0 to indicate that
     the element was not inserted into the buffer.

     XXX: there is a potential risk for a race condition here, because
     the ->get_ptr field may be written concurrently by the
     ringbuf_get() function. To avoid this, access to ->get_ptr must
     be atomic. We use an uint8_t type, which makes access atomic on
     most platforms, but C does not guarantee this.
  */
  if(((r->put_ptr - r->get_ptr) & r->mask) == r->mask) {
    return 0;
  }
  r->data[r->put_ptr] = c;
  r->put_ptr = (r->put_ptr + 1) & r->mask;
  return 1;
}
/*---------------------------------------------------------------------------*/
int
ringbuf_get(struct ringbuf *r)
{
  uint8_t c;
  
  c = r->data[r->get_ptr];
  r->get_ptr = (r->get_ptr + 1) & r->mask;
  return c;
}
/*---------------------------------------------------------------------------*/
int
ringbuf_get_existcheck(struct ringbuf *r)
{
  uint8_t c;
  
  /* Check if there are bytes in the buffer. If so, we return the
     first one and increase the pointer. If there are no bytes left, we
     return -1.

     XXX: there is a potential risk for a race condition here, because
     the ->put_ptr field may be written concurrently by the
     ringbuf_put() function. To avoid this, access to ->get_ptr must
     be atomic. We use an uint8_t type, which makes access atomic on
     most platforms, but C does not guarantee this.
  */
  if(((r->put_ptr - r->get_ptr) & r->mask) > 0) {
    c = r->data[r->get_ptr];
    r->get_ptr = (r->get_ptr + 1) & r->mask;
    return c;
  } else {
    return -1;
  }
}
/*---------------------------------------------------------------------------*/
int
ringbuf_size(struct ringbuf *r)
{
  return r->mask + 1;
}
/*---------------------------------------------------------------------------*/
int
ringbuf_elements(struct ringbuf *r)
{
  return (r->put_ptr - r->get_ptr) & r->mask;
}
/*---------------------------------------------------------------------------*/
