MogleyC/Gentlman20211010/Ses/G5.3B_nRF/SRC/Module_Ble.h

#ifndef MODULE_BLE_H
#define MODULE_BLE_H

#ifdef __cplusplus
extern "C"
{
#endif

	//#include <stdbool.h>
	//#include <stdint.h>

	void ble_Init();

#ifdef __cplusplus
}
#endif //__cplusplus

#endif // MODULE_UART_H
