MogleyC/Gentlman20211010/Ses/G5.3B_nRF/SRC/Module_Clock.h

#ifndef MODULE_CLOCK_H
#define MODULE_CLOCK_H

#ifdef __cplusplus
extern "C"
{
#endif

#include <stdint.h>

	void nrf_clock_init();
	void clock_init(uint8_t HFCLKtype, uint8_t LFCLKtype);

#ifdef __cplusplus
}
#endif //__cplusplus

#endif // MODULE_GPIO_H
